IURIIVas/RVisitor/soft/src/tasks/motion_control/motion_control.h

/// \file motion_control.h
/// \brief mmm header files
/// \author 1jura.vas@gmail.com
///
/// \details
///

//--------------------------------------------------- Include guards ---------------------------------------------------

#ifndef MOTION_CONTROL_H_
#define MOTION_CONTROL_H_

//----------------------------------------------------- Includes -------------------------------------------------------

#include "global_inc.h"
#include "dc_motor_controller.h"

//------------------------------------------------------ Macros --------------------------------------------------------

//----------------------------------------------------- Typedefs -------------------------------------------------------

//---------------------------------------------------- Variables -------------------------------------------------------

extern TaskHandle_t motion_control_task_handler;

//------------------------------------------------ Function prototypes -------------------------------------------------

void motion_control_task_init(void);


#endif /* MOTION_CONTROL_H_ */
