IURIIVas/RVisitor/hardware/ch32v30x.h

/********************************** (C) COPYRIGHT  *******************************
* File Name          : ch32v30x.h
* Author             : WCH
* Version            : V1.0.0
* Date               : 2021/06/06
* Description        : CH32V30x Device Peripheral Access Layer Header File.
*********************************************************************************
* Copyright (c) 2021 Nanjing Qinheng Microelectronics Co., Ltd.
* Attention: This software (modified or not) and binary are used for 
* microcontroller manufactured by Nanjing Qinheng Microelectronics.
*******************************************************************************/  
#ifndef __CH32V30x_H
#define __CH32V30x_H

#ifdef __cplusplus
 extern "C" {
#endif 

#if !defined(CH32V30x_D8) && !defined(CH32V30x_D8C)
//#define CH32V30x_D8              /* CH32V303x */
#define CH32V30x_D8C             /* CH32V307x-CH32V305x */

#endif
  
#define __MPU_PRESENT             0 /* Other CH32 devices does not provide an MPU */
#define __Vendor_SysTickConfig    0 /* Set to 1 if different SysTick Config is used */	 
	 
#define HSE_VALUE    ((uint32_t)8000000) /* Value of the External oscillator in Hz */

/* In the following line adjust the External High Speed oscillator (HSE) Startup Timeout value */
#define HSE_STARTUP_TIMEOUT   ((uint16_t)0x1000) /* Time out for HSE start up */

#define HSI_VALUE    ((uint32_t)8000000) /* Value of the Internal oscillator in Hz */

/* CH32V30x Standard Peripheral Library version number */
#define __CH32V30x_STDPERIPH_VERSION_MAIN   (0x02) /* [15:8] main version */
#define __CH32V30x_STDPERIPH_VERSION_SUB    (0x01) /* [7:0] sub version */
#define __CH32V30x_STDPERIPH_VERSION        ( (__CH32V30x_STDPERIPH_VERSION_MAIN << 8)\
                                             |(__CH32V30x_STDPERIPH_VERSION_SUB << 0))


/* Interrupt Number Definition, according to the selected device */	 
typedef enum IRQn
{
 /******  RISC-V Processor Exceptions Numbers *******************************************************/
  NonMaskableInt_IRQn         = 2,       /* 2 Non Maskable Interrupt                             */
  EXC_IRQn                    = 3,       /* 3 Exception Interrupt                                */
  Ecall_M_Mode_IRQn           = 5,       /* 5 Ecall M Mode Interrupt                             */
  Ecall_U_Mode_IRQn           = 8,       /* 8 Ecall U Mode Interrupt                             */
  Break_Point_IRQn            = 9,       /* 9 Break Point Interrupt                              */
  SysTicK_IRQn                = 12,      /* 12 System timer Interrupt                            */
  Software_IRQn               = 14,      /* 14 software Interrupt                                */

 /******  RISC-V specific Interrupt Numbers *********************************************************/
  WWDG_IRQn                   = 16,      /* Window WatchDog Interrupt                            */
  PVD_IRQn                    = 17,      /* PVD through EXTI Line detection Interrupt            */
  TAMPER_IRQn                 = 18,      /* Tamper Interrupt                                     */
  RTC_IRQn                    = 19,      /* RTC global Interrupt                                 */
  FLASH_IRQn                  = 20,      /* FLASH global Interrupt                               */
  RCC_IRQn                    = 21,      /* RCC global Interrupt                                 */
  EXTI0_IRQn                  = 22,      /* EXTI Line0 Interrupt                                 */
  EXTI1_IRQn                  = 23,      /* EXTI Line1 Interrupt                                 */
  EXTI2_IRQn                  = 24,      /* EXTI Line2 Interrupt                                 */
  EXTI3_IRQn                  = 25,      /* EXTI Line3 Interrupt                                 */
  EXTI4_IRQn                  = 26,      /* EXTI Line4 Interrupt                                 */
  DMA1_Channel1_IRQn          = 27,      /* DMA1 Channel 1 global Interrupt                      */
  DMA1_Channel2_IRQn          = 28,      /* DMA1 Channel 2 global Interrupt                      */
  DMA1_Channel3_IRQn          = 29,      /* DMA1 Channel 3 global Interrupt                      */
  DMA1_Channel4_IRQn          = 30,      /* DMA1 Channel 4 global Interrupt                      */
  DMA1_Channel5_IRQn          = 31,      /* DMA1 Channel 5 global Interrupt                      */
  DMA1_Channel6_IRQn          = 32,      /* DMA1 Channel 6 global Interrupt                      */
  DMA1_Channel7_IRQn          = 33,      /* DMA1 Channel 7 global Interrupt                      */
  ADC_IRQn                    = 34,      /* ADC1 and ADC2 global Interrupt                       */
  USB_HP_CAN1_TX_IRQn         = 35,      /* USB Device High Priority or CAN1 TX Interrupts       */
  USB_LP_CAN1_RX0_IRQn        = 36,      /* USB Device Low Priority or CAN1 RX0 Interrupts       */
  CAN1_RX1_IRQn               = 37,      /* CAN1 RX1 Interrupt                                   */
  CAN1_SCE_IRQn               = 38,      /* CAN1 SCE Interrupt                                   */
  EXTI9_5_IRQn                = 39,      /* External Line[9:5] Interrupts                        */
  TIM1_BRK_IRQn               = 40,      /* TIM1 Break Interrupt                                 */
  TIM1_UP_IRQn                = 41,      /* TIM1 Update Interrupt                                */
  TIM1_TRG_COM_IRQn           = 42,      /* TIM1 Trigger and Commutation Interrupt               */
  TIM1_CC_IRQn                = 43,      /* TIM1 Capture Compare Interrupt                       */
  TIM2_IRQn                   = 44,      /* TIM2 global Interrupt                                */
  TIM3_IRQn                   = 45,      /* TIM3 global Interrupt                                */
  TIM4_IRQn                   = 46,      /* TIM4 global Interrupt                                */
  I2C1_EV_IRQn                = 47,      /* I2C1 Event Interrupt                                 */
  I2C1_ER_IRQn                = 48,      /* I2C1 Error Interrupt                                 */
  I2C2_EV_IRQn                = 49,      /* I2C2 Event Interrupt                                 */
  I2C2_ER_IRQn                = 50,      /* I2C2 Error Interrupt                                 */
  SPI1_IRQn                   = 51,      /* SPI1 global Interrupt                                */
  SPI2_IRQn                   = 52,      /* SPI2 global Interrupt                                */
  USART1_IRQn                 = 53,      /* USART1 global Interrupt                              */
  USART2_IRQn                 = 54,      /* USART2 global Interrupt                              */
  USART3_IRQn                 = 55,      /* USART3 global Interrupt                              */
  EXTI15_10_IRQn              = 56,      /* External Line[15:10] Interrupts                      */
  RTCAlarm_IRQn               = 57,      /* RTC Alarm through EXTI Line Interrupt                */

#ifdef CH32V30x_D8
  TIM8_BRK_IRQn               = 59,      /* TIM8 Break Interrupt                                 */
  TIM8_UP_IRQn                = 60,      /* TIM8 Update Interrupt                                */
  TIM8_TRG_COM_IRQn           = 61,      /* TIM8 Trigger and Commutation Interrupt               */
  TIM8_CC_IRQn                = 62,      /* TIM8 Capture Compare Interrupt                       */
  RNG_IRQn                    = 63,      /* RNG global Interrupt                                 */
  FSMC_IRQn                   = 64,      /* FSMC global Interrupt                                */
  SDIO_IRQn                   = 65,      /* SDIO global Interrupt                                */
  TIM5_IRQn                   = 66,      /* TIM5 global Interrupt                                */
  SPI3_IRQn                   = 67,      /* SPI3 global Interrupt                                */
  UART4_IRQn                  = 68,      /* UART4 global Interrupt                               */
  UART5_IRQn                  = 69,      /* UART5 global Interrupt                               */
  TIM6_IRQn                   = 70,      /* TIM6 global Interrupt                                */
  TIM7_IRQn                   = 71,      /* TIM7 global Interrupt                                */
  DMA2_Channel1_IRQn          = 72,      /* DMA2 Channel 1 global Interrupt                      */
  DMA2_Channel2_IRQn          = 73,      /* DMA2 Channel 2 global Interrupt                      */
  DMA2_Channel3_IRQn          = 74,      /* DMA2 Channel 3 global Interrupt                      */
  DMA2_Channel4_IRQn          = 75,      /* DMA2 Channel 4 global Interrupt                      */
  DMA2_Channel5_IRQn          = 76,      /* DMA2 Channel 5 global Interrupt                      */
  OTG_FS_IRQn                 = 83,      /* OTGFS global Interrupt                               */
  UART6_IRQn                  = 87,      /* UART6 global Interrupt                               */
  UART7_IRQn                  = 88,      /* UART7 global Interrupt                               */
  UART8_IRQn                  = 89,      /* UART8 global Interrupt                               */
  TIM9_BRK_IRQn               = 90,      /* TIM9 Break Interrupt                                 */
  TIM9_UP_IRQn                = 91,      /* TIM9 Update Interrupt                                */
  TIM9_TRG_COM_IRQn           = 92,      /* TIM9 Trigger and Commutation Interrupt               */
  TIM9_CC_IRQn                = 93,      /* TIM9 Capture Compare Interrupt                       */
  TIM10_BRK_IRQn              = 94,      /* TIM10 Break Interrupt                                */
  TIM10_UP_IRQn               = 95,      /* TIM10 Update Interrupt                               */
  TIM10_TRG_COM_IRQn          = 96,      /* TIM10 Trigger and Commutation Interrupt              */
  TIM10_CC_IRQn               = 97,      /* TIM10 Capture Compare Interrupt                      */
  DMA2_Channel6_IRQn          = 98,      /* DMA2 Channel 6 global Interrupt                      */
  DMA2_Channel7_IRQn          = 99,      /* DMA2 Channel 7 global Interrupt                      */
  DMA2_Channel8_IRQn          = 100,     /* DMA2 Channel 8 global Interrupt                      */
  DMA2_Channel9_IRQn          = 101,     /* DMA2 Channel 9 global Interrupt                      */
  DMA2_Channel10_IRQn         = 102,     /* DMA2 Channel 10 global Interrupt                     */
  DMA2_Channel11_IRQn         = 103,     /* DMA2 Channel 11 global Interrupt                     */

#elif defined  (CH32V30x_D8C)
  USBWakeUp_IRQn              = 58,      /* USB Device WakeUp from suspend through EXTI Line Interrupt */
  TIM8_BRK_IRQn               = 59,      /* TIM8 Break Interrupt                                 */
  TIM8_UP_IRQn                = 60,      /* TIM8 Update Interrupt                                */
  TIM8_TRG_COM_IRQn           = 61,      /* TIM8 Trigger and Commutation Interrupt               */
  TIM8_CC_IRQn                = 62,      /* TIM8 Capture Compare Interrupt                       */
  RNG_IRQn                    = 63,      /* RNG global Interrupt                                 */
  FSMC_IRQn                   = 64,      /* FSMC global Interrupt                                */
  SDIO_IRQn                   = 65,      /* SDIO global Interrupt                                */
  TIM5_IRQn                   = 66,      /* TIM5 global Interrupt                                */
  SPI3_IRQn                   = 67,      /* SPI3 global Interrupt                                */
  UART4_IRQn                  = 68,      /* UART4 global Interrupt                               */
  UART5_IRQn                  = 69,      /* UART5 global Interrupt                               */
  TIM6_IRQn                   = 70,      /* TIM6 global Interrupt                                */
  TIM7_IRQn                   = 71,      /* TIM7 global Interrupt                                */
  DMA2_Channel1_IRQn          = 72,      /* DMA2 Channel 1 global Interrupt                      */
  DMA2_Channel2_IRQn          = 73,      /* DMA2 Channel 2 global Interrupt                      */
  DMA2_Channel3_IRQn          = 74,      /* DMA2 Channel 3 global Interrupt                      */
  DMA2_Channel4_IRQn          = 75,      /* DMA2 Channel 4 global Interrupt                      */
  DMA2_Channel5_IRQn          = 76,      /* DMA2 Channel 5 global Interrupt                      */
  ETH_IRQn                    = 77,      /* ETH global Interrupt                                 */
  ETH_WKUP_IRQn               = 78,      /* ETH WakeUp Interrupt                                 */
  CAN2_TX_IRQn                = 79,      /* CAN2 TX Interrupts                                   */
  CAN2_RX0_IRQn               = 80,      /* CAN2 RX0 Interrupts                                  */
  CAN2_RX1_IRQn               = 81,      /* CAN2 RX1 Interrupt                                   */
  CAN2_SCE_IRQn               = 82,      /* CAN2 SCE Interrupt                                   */
  OTG_FS_IRQn                 = 83,      /* OTGFS global Interrupt                               */
  USBHSWakeup_IRQn            = 84,      /* USBHS WakeUp Interrupt                               */
  USBHS_IRQn                  = 85,      /* USBHS global Interrupt                               */
  DVP_IRQn                    = 86,      /* DVP global Interrupt                                 */
  UART6_IRQn                  = 87,      /* UART6 global Interrupt                               */
  UART7_IRQn                  = 88,      /* UART7 global Interrupt                               */
  UART8_IRQn                  = 89,      /* UART8 global Interrupt                               */
  TIM9_BRK_IRQn               = 90,      /* TIM9 Break Interrupt                                 */
  TIM9_UP_IRQn                = 91,      /* TIM9 Update Interrupt                                */
  TIM9_TRG_COM_IRQn           = 92,      /* TIM9 Trigger and Commutation Interrupt               */
  TIM9_CC_IRQn                = 93,      /* TIM9 Capture Compare Interrupt                       */
  TIM10_BRK_IRQn              = 94,      /* TIM10 Break Interrupt                                */
  TIM10_UP_IRQn               = 95,      /* TIM10 Update Interrupt                               */
  TIM10_TRG_COM_IRQn          = 96,      /* TIM10 Trigger and Commutation Interrupt              */
  TIM10_CC_IRQn               = 97,      /* TIM10 Capture Compare Interrupt                      */
  DMA2_Channel6_IRQn          = 98,      /* DMA2 Channel 6 global Interrupt                      */
  DMA2_Channel7_IRQn          = 99,      /* DMA2 Channel 7 global Interrupt                      */
  DMA2_Channel8_IRQn          = 100,     /* DMA2 Channel 8 global Interrupt                      */
  DMA2_Channel9_IRQn          = 101,     /* DMA2 Channel 9 global Interrupt                      */
  DMA2_Channel10_IRQn         = 102,     /* DMA2 Channel 10 global Interrupt                     */
  DMA2_Channel11_IRQn         = 103,     /* DMA2 Channel 11 global Interrupt                     */

#endif
} irqn_e;

#define HardFault_IRQn   EXC_IRQn
#define ADC1_2_IRQn      ADC_IRQn


#include <stdint.h>
#include "core_riscv.h"
#include "system_ch32v30x.h"


/* Standard Peripheral Library old definitions (maintained for legacy purpose) */
#define HSI_Value            HSI_VALUE 
#define HSE_Value            HSE_VALUE
#define HSEStartUp_TimeOut   HSE_STARTUP_TIMEOUT

/* Analog to Digital Converter */
typedef struct
{
  __RW uint32_t STATR;
  __RW uint32_t CTLR1;
  __RW uint32_t CTLR2;
  __RW uint32_t SAMPTR1;
  __RW uint32_t SAMPTR2;
  __RW uint32_t IOFR1;
  __RW uint32_t IOFR2;
  __RW uint32_t IOFR3;
  __RW uint32_t IOFR4;
  __RW uint32_t WDHTR;
  __RW uint32_t WDLTR;
  __RW uint32_t RSQR1;
  __RW uint32_t RSQR2;
  __RW uint32_t RSQR3;
  __RW uint32_t ISQR;
  __RW uint32_t IDATAR1;
  __RW uint32_t IDATAR2;
  __RW uint32_t IDATAR3;
  __RW uint32_t IDATAR4;
  __RW uint32_t RDATAR;
} ADC_TypeDef;

/* Backup Registers */
typedef struct
{
  uint32_t  RESERVED0;
  __RW uint16_t DATAR1;
  uint16_t  RESERVED1;
  __RW uint16_t DATAR2;
  uint16_t  RESERVED2;
  __RW uint16_t DATAR3;
  uint16_t  RESERVED3;
  __RW uint16_t DATAR4;
  uint16_t  RESERVED4;
  __RW uint16_t DATAR5;
  uint16_t  RESERVED5;
  __RW uint16_t DATAR6;
  uint16_t  RESERVED6;
  __RW uint16_t DATAR7;
  uint16_t  RESERVED7;
  __RW uint16_t DATAR8;
  uint16_t  RESERVED8;
  __RW uint16_t DATAR9;
  uint16_t  RESERVED9;
  __RW uint16_t DATAR10;
  uint16_t  RESERVED10; 
  __RW uint16_t OCTLR;
  uint16_t  RESERVED11;
  __RW uint16_t TPCTLR;
  uint16_t  RESERVED12;
  __RW uint16_t TPCSR;
  uint16_t  RESERVED13[5];
  __RW uint16_t DATAR11;
  uint16_t  RESERVED14;
  __RW uint16_t DATAR12;
  uint16_t  RESERVED15;
  __RW uint16_t DATAR13;
  uint16_t  RESERVED16;
  __RW uint16_t DATAR14;
  uint16_t  RESERVED17;
  __RW uint16_t DATAR15;
  uint16_t  RESERVED18;
  __RW uint16_t DATAR16;
  uint16_t  RESERVED19;
  __RW uint16_t DATAR17;
  uint16_t  RESERVED20;
  __RW uint16_t DATAR18;
  uint16_t  RESERVED21;
  __RW uint16_t DATAR19;
  uint16_t  RESERVED22;
  __RW uint16_t DATAR20;
  uint16_t  RESERVED23;
  __RW uint16_t DATAR21;
  uint16_t  RESERVED24;
  __RW uint16_t DATAR22;
  uint16_t  RESERVED25;
  __RW uint16_t DATAR23;
  uint16_t  RESERVED26;
  __RW uint16_t DATAR24;
  uint16_t  RESERVED27;
  __RW uint16_t DATAR25;
  uint16_t  RESERVED28;
  __RW uint16_t DATAR26;
  uint16_t  RESERVED29;
  __RW uint16_t DATAR27;
  uint16_t  RESERVED30;
  __RW uint16_t DATAR28;
  uint16_t  RESERVED31;
  __RW uint16_t DATAR29;
  uint16_t  RESERVED32;
  __RW uint16_t DATAR30;
  uint16_t  RESERVED33; 
  __RW uint16_t DATAR31;
  uint16_t  RESERVED34;
  __RW uint16_t DATAR32;
  uint16_t  RESERVED35;
  __RW uint16_t DATAR33;
  uint16_t  RESERVED36;
  __RW uint16_t DATAR34;
  uint16_t  RESERVED37;
  __RW uint16_t DATAR35;
  uint16_t  RESERVED38;
  __RW uint16_t DATAR36;
  uint16_t  RESERVED39;
  __RW uint16_t DATAR37;
  uint16_t  RESERVED40;
  __RW uint16_t DATAR38;
  uint16_t  RESERVED41;
  __RW uint16_t DATAR39;
  uint16_t  RESERVED42;
  __RW uint16_t DATAR40;
  uint16_t  RESERVED43;
  __RW uint16_t DATAR41;
  uint16_t  RESERVED44;
  __RW uint16_t DATAR42;
  uint16_t  RESERVED45;    
} BKP_TypeDef;

/* Controller Area Network TxMailBox */
typedef struct
{
  __RW uint32_t TXMIR;
  __RW uint32_t TXMDTR;
  __RW uint32_t TXMDLR;
  __RW uint32_t TXMDHR;
} CAN_TxMailBox_TypeDef;

/* Controller Area Network FIFOMailBox */ 
typedef struct
{
  __RW uint32_t RXMIR;
  __RW uint32_t RXMDTR;
  __RW uint32_t RXMDLR;
  __RW uint32_t RXMDHR;
} CAN_FIFOMailBox_TypeDef;

/* Controller Area Network FilterRegister */  
typedef struct
{
  __RW uint32_t FR1;
  __RW uint32_t FR2;
} CAN_FilterRegister_TypeDef;

/* Controller Area Network */  
typedef struct
{
  __RW uint32_t CTLR;
  __RW uint32_t STATR;
  __RW uint32_t TSTATR;
  __RW uint32_t RFIFO0;
  __RW uint32_t RFIFO1;
  __RW uint32_t INTENR;
  __RW uint32_t ERRSR;
  __RW uint32_t BTIMR;
  uint32_t  RESERVED0[88];
  CAN_TxMailBox_TypeDef sTxMailBox[3];
  CAN_FIFOMailBox_TypeDef sFIFOMailBox[2];
  uint32_t  RESERVED1[12];
  __RW uint32_t FCTLR;
  __RW uint32_t FMCFGR;
  uint32_t  RESERVED2;
  __RW uint32_t FSCFGR;
  uint32_t  RESERVED3;
  __RW uint32_t FAFIFOR;
  uint32_t  RESERVED4;
  __RW uint32_t FWR;
  uint32_t  RESERVED5[8];
  CAN_FilterRegister_TypeDef sFilterRegister[28];
} CAN_TypeDef;

/* CRC Calculation Unit */
typedef struct
{
  __RW uint32_t DATAR;
  __RW uint8_t  IDATAR;
  uint8_t   RESERVED0;
  uint16_t  RESERVED1;
  __RW uint32_t CTLR;
} CRC_TypeDef;

/* Digital to Analog Converter */
typedef struct
{
  __RW uint32_t CTLR;
  __RW uint32_t SWTR;
  __RW uint32_t R12BDHR1;
  __RW uint32_t L12BDHR1;
  __RW uint32_t R8BDHR1;
  __RW uint32_t R12BDHR2;
  __RW uint32_t L12BDHR2;
  __RW uint32_t R8BDHR2;
  __RW uint32_t RD12BDHR;
  __RW uint32_t LD12BDHR;
  __RW uint32_t RD8BDHR;
  __RW uint32_t DOR1;
  __RW uint32_t DOR2;
} DAC_TypeDef;

/* DMA Channel Controller */
typedef struct
{
  __RW uint32_t CFGR;
  __RW uint32_t CNTR;
  __RW uint32_t PADDR;
  __RW uint32_t MADDR;
} DMA_Channel_TypeDef;

/* DMA Controller */
typedef struct
{
  __RW uint32_t INTFR;
  __RW uint32_t INTFCR;
} DMA_TypeDef;

/* External Interrupt/Event Controller */
typedef struct
{
  __RW uint32_t INTENR; 
  __RW uint32_t EVENR;   
  __RW uint32_t RTENR;   
  __RW uint32_t FTENR;   
  __RW uint32_t SWIEVR;  
  __RW uint32_t INTFR;   
} EXTI_TypeDef;

/* FLASH Registers */
typedef struct
{
  __RW uint32_t ACTLR;
  __RW uint32_t KEYR;
  __RW uint32_t OBKEYR;
  __RW uint32_t STATR;
  __RW uint32_t CTLR;
  __RW uint32_t ADDR;
  __RW uint32_t RESERVED;
  __RW uint32_t OBR;
  __RW uint32_t WPR;
  __RW uint32_t MODEKEYR;
} FLASH_TypeDef;

/* Option Bytes Registers */  
typedef struct
{
  __RW uint16_t RDPR;
  __RW uint16_t USER;
  __RW uint16_t Data0;
  __RW uint16_t Data1;
  __RW uint16_t WRPR0;
  __RW uint16_t WRPR1;
  __RW uint16_t WRPR2;
  __RW uint16_t WRPR3;
} OB_TypeDef;

/* FSMC Bank1 Registers */ 
typedef struct
{
  __RW uint32_t BTCR[8];
} FSMC_Bank1_TypeDef;

/* FSMC Bank1E Registers */ 
typedef struct
{
  __RW uint32_t BWTR[7];
} FSMC_Bank1E_TypeDef;

/* FSMC Bank2 Registers */ 
typedef struct
{
  __RW uint32_t PCR2;
  __RW uint32_t SR2;
  __RW uint32_t PMEM2;
  __RW uint32_t PATT2;
  uint32_t  RESERVED0;
  __RW uint32_t ECCR2;
} FSMC_Bank2_TypeDef;

/* General Purpose I/O */
typedef struct
{
  __RW uint32_t CFGLR;
  __RW uint32_t CFGHR;
  __RW uint32_t INDR;
  __RW uint32_t OUTDR;
  __RW uint32_t BSHR;
  __RW uint32_t BCR;
  __RW uint32_t LCKR;
} gpio_s;

/* Alternate Function I/O */
typedef struct
{
  __RW uint32_t ECR;
  __RW uint32_t PCFR1;
  __RW uint32_t EXTICR[4];
  uint32_t RESERVED0;
  __RW uint32_t PCFR2;  
} AFIO_TypeDef;

/* Inter Integrated Circuit Interface */
typedef struct
{
  __RW uint16_t CTLR1;
  uint16_t  RESERVED0;
  __RW uint16_t CTLR2;
  uint16_t  RESERVED1;
  __RW uint16_t OADDR1;
  uint16_t  RESERVED2;
  __RW uint16_t OADDR2;
  uint16_t  RESERVED3;
  __RW uint16_t DATAR;
  uint16_t  RESERVED4;
  __RW uint16_t STAR1;
  uint16_t  RESERVED5;
  __RW uint16_t STAR2;
  uint16_t  RESERVED6;
  __RW uint16_t CKCFGR;
  uint16_t  RESERVED7;
  __RW uint16_t RTR;
  uint16_t  RESERVED8;
} i2c_s;

/* Independent WatchDog */
typedef struct
{
  __RW uint32_t CTLR;
  __RW uint32_t PSCR;
  __RW uint32_t RLDR;
  __RW uint32_t STATR;
} IWDG_TypeDef;

/* Power Control */
typedef struct
{
  __RW uint32_t CTLR;
  __RW uint32_t CSR;
} PWR_TypeDef;

/* Reset and Clock Control */
typedef struct
{
  __RW uint32_t CTLR;
  __RW uint32_t CFGR0;
  __RW uint32_t INTR;
  __RW uint32_t APB2PRSTR;
  __RW uint32_t APB1PRSTR;
  __RW uint32_t AHBPCENR;
  __RW uint32_t APB2PCENR;
  __RW uint32_t APB1PCENR;
  __RW uint32_t BDCTLR;
  __RW uint32_t RSTSCKR;

  __RW uint32_t AHBRSTR;
  __RW uint32_t CFGR2;
} RCC_TypeDef;

/* Real-Time Clock */
typedef struct
{
  __RW uint16_t CTLRH;
  uint16_t  RESERVED0;
  __RW uint16_t CTLRL;
  uint16_t  RESERVED1;
  __RW uint16_t PSCRH;
  uint16_t  RESERVED2;
  __RW uint16_t PSCRL;
  uint16_t  RESERVED3;
  __RW uint16_t DIVH;
  uint16_t  RESERVED4;
  __RW uint16_t DIVL;
  uint16_t  RESERVED5;
  __RW uint16_t CNTH;
  uint16_t  RESERVED6;
  __RW uint16_t CNTL;
  uint16_t  RESERVED7;
  __RW uint16_t ALRMH;
  uint16_t  RESERVED8;
  __RW uint16_t ALRML;
  uint16_t  RESERVED9;
} RTC_TypeDef;

/* SDIO Registers */ 
typedef struct
{
  __RW uint32_t POWER;
  __RW uint32_t CLKCR;
  __RW uint32_t ARG;
  __RW uint32_t CMD;
  __RO uint32_t RESPCMD;
  __RO uint32_t RESP1;
  __RO uint32_t RESP2;
  __RO uint32_t RESP3;
  __RO uint32_t RESP4;
  __RW uint32_t DTIMER;
  __RW uint32_t DLEN;
  __RW uint32_t DCTRL;
  __RO uint32_t DCOUNT;
  __RO uint32_t STA;
  __RW uint32_t ICR;
  __RW uint32_t MASK;
  uint32_t  RESERVED0[2];
  __RO uint32_t FIFOCNT;
  uint32_t  RESERVED1[13];
  __RW uint32_t FIFO;
} SDIO_TypeDef;

/* Serial Peripheral Interface */
typedef struct
{
  __RW uint16_t CTLR1;
  uint16_t  RESERVED0;
  __RW uint16_t CTLR2;
  uint16_t  RESERVED1;
  __RW uint16_t STATR;
  uint16_t  RESERVED2;
  __RW uint16_t DATAR;
  uint16_t  RESERVED3;
  __RW uint16_t CRCR;
  uint16_t  RESERVED4;
  __RW uint16_t RCRCR;
  uint16_t  RESERVED5;
  __RW uint16_t TCRCR;
  uint16_t  RESERVED6;
  __RW uint16_t I2SCFGR;
  uint16_t  RESERVED7;
  __RW uint16_t I2SPR;
  uint16_t  RESERVED8;
  __RW uint16_t HSCR;
  uint16_t  RESERVED9;
} spi_s;

/* TIM */
typedef struct
{
  __RW uint16_t CTLR1;
  uint16_t  RESERVED0;
  __RW uint16_t CTLR2;
  uint16_t  RESERVED1;
  __RW uint16_t SMCFGR;
  uint16_t  RESERVED2;
  __RW uint16_t DMAINTENR;
  uint16_t  RESERVED3;
  __RW uint16_t INTFR;
  uint16_t  RESERVED4;
  __RW uint16_t SWEVGR;
  uint16_t  RESERVED5;
  __RW uint16_t CHCTLR1;
  uint16_t  RESERVED6;
  __RW uint16_t CHCTLR2;
  uint16_t  RESERVED7;
  __RW uint16_t CCER;
  uint16_t  RESERVED8;
  __RW uint16_t CNT;
  uint16_t  RESERVED9;
  __RW uint16_t PSC;
  uint16_t  RESERVED10;
  __RW uint16_t ATRLR;
  uint16_t  RESERVED11;
  __RW uint16_t RPTCR;
  uint16_t  RESERVED12;
  __RW uint16_t CH1CVR;
  uint16_t  RESERVED13;
  __RW uint16_t CH2CVR;
  uint16_t  RESERVED14;
  __RW uint16_t CH3CVR;
  uint16_t  RESERVED15;
  __RW uint16_t CH4CVR;
  uint16_t  RESERVED16;
  __RW uint16_t BDTR;
  uint16_t  RESERVED17;
  __RW uint16_t DMACFGR;
  uint16_t  RESERVED18;
  __RW uint16_t DMAADR;
  uint16_t  RESERVED19;
} TIM_TypeDef;

/* Universal Synchronous Asynchronous Receiver Transmitter */
typedef struct
{
  __RW uint16_t STATR;
  uint16_t  RESERVED0;
  __RW uint16_t DATAR;
  uint16_t  RESERVED1;
  __RW uint16_t BRR;
  uint16_t  RESERVED2;
  __RW uint16_t CTLR1;
  uint16_t  RESERVED3;
  __RW uint16_t CTLR2;
  uint16_t  RESERVED4;
  __RW uint16_t CTLR3;
  uint16_t  RESERVED5;
  __RW uint16_t GPR;
  uint16_t  RESERVED6;
} USART_TypeDef;

/* Window WatchDog */
typedef struct
{
  __RW uint32_t CTLR;
  __RW uint32_t CFGR;
  __RW uint32_t STATR;
} WWDG_TypeDef;

/* Enhanced Registers */
typedef struct
{
  __RW uint32_t EXTEN_CTR;
} EXTEN_TypeDef;

/* OPA Registers */
typedef struct
{
  __RW uint32_t CR;
} OPA_TypeDef;

/* RNG Registers */
typedef struct
{
  __RW uint32_t CR;
  __RW uint32_t SR;
  __RW uint32_t DR;
} RNG_TypeDef;

/* DVP Registers */
typedef struct
{
  __RW uint8_t CR0;
  __RW uint8_t CR1;
  __RW uint8_t IER;
  __RW uint8_t Reserved0;        
  __RW uint16_t ROW_NUM;
  __RW uint16_t COL_NUM;
  __RW uint32_t DMA_BUF0;
  __RW uint32_t DMA_BUF1;
  __RW uint8_t IFR;
  __RW uint8_t STATUS;
  __RW uint16_t Reserved1;            
  __RW uint16_t ROW_CNT;
  __RW uint16_t Reserved2;           
  __RW uint16_t HOFFCNT;
  __RW uint16_t VST;
  __RW uint16_t CAPCNT;
  __RW uint16_t VLINE;
  __RW uint32_t DR;
} DVP_TypeDef;

/* USBHS Registers */
typedef struct
{
  __RW uint8_t  CONTROL;
  __RW uint8_t  HOST_CTRL;
  __RW uint8_t  INT_EN;
  __RW uint8_t  DEV_AD;
  __RW uint16_t FRAME_NO;
  __RW uint8_t  SUSPEND;
  __RW uint8_t  RESERVED0;
  __RW uint8_t  SPEED_TYPE;
  __RW uint8_t  MIS_ST;
  __RW uint8_t  INT_FG;
  __RW uint8_t  INT_ST;
  __RW uint16_t RX_LEN;
  __RW uint16_t RESERVED1;
  __RW uint32_t ENDP_CONFIG;
  __RW uint32_t ENDP_TYPE;
  __RW uint32_t BUF_MODE;
  __RW uint32_t UEP0_DMA;               
  __RW uint32_t UEP1_RX_DMA;       
  __RW uint32_t UEP2_RX_DMA;       
  __RW uint32_t UEP3_RX_DMA;       
  __RW uint32_t UEP4_RX_DMA;       
  __RW uint32_t UEP5_RX_DMA;       
  __RW uint32_t UEP6_RX_DMA;       
  __RW uint32_t UEP7_RX_DMA;       
  __RW uint32_t UEP8_RX_DMA;      
  __RW uint32_t UEP9_RX_DMA;       
  __RW uint32_t UEP10_RX_DMA;      
  __RW uint32_t UEP11_RX_DMA;      
  __RW uint32_t UEP12_RX_DMA;      
  __RW uint32_t UEP13_RX_DMA;      
  __RW uint32_t UEP14_RX_DMA;      
  __RW uint32_t UEP15_RX_DMA;      
  __RW uint32_t UEP1_TX_DMA;       
  __RW uint32_t UEP2_TX_DMA;       
  __RW uint32_t UEP3_TX_DMA;       
  __RW uint32_t UEP4_TX_DMA;       
  __RW uint32_t UEP5_TX_DMA;      
  __RW uint32_t UEP6_TX_DMA;      
  __RW uint32_t UEP7_TX_DMA;       
  __RW uint32_t UEP8_TX_DMA;      
  __RW uint32_t UEP9_TX_DMA;       
  __RW uint32_t UEP10_TX_DMA;      
  __RW uint32_t UEP11_TX_DMA;      
  __RW uint32_t UEP12_TX_DMA;    
  __RW uint32_t UEP13_TX_DMA;      
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
    __RW uint32_t RESERVED42;
    __RW uint32_t RESERVED43;
    __RW uint32_t RESERVED44;
    __RW uint32_t RESERVED45;
    __RW uint32_t RESERVED46;
    __RW uint32_t RESERVED47;
    __RW uint32_t RESERVED48;
    __RW uint32_t RESERVED49;
    __RW uint8_t  HOST_EP_PID;
    __RW uint8_t  RESERVED50;
    __RW uint8_t  RESERVED51;
    __RW uint8_t  HOST_RX_CTRL;
    __RW uint16_t HOST_TX_LEN;
    __RW uint8_t  HOST_TX_CTRL;
    __RW uint8_t  RESERVED52;
    __RW uint16_t HOST_SPLIT_DATA;
} USBHSH_TypeDef;


/* USBOTG_FS Registers */
typedef struct
{
   __RW uint8_t  BASE_CTRL;
   __RW uint8_t  UDEV_CTRL;
   __RW uint8_t  INT_EN;
   __RW uint8_t  DEV_ADDR;
   __RW uint8_t  Reserve0;
   __RW uint8_t  MIS_ST;
   __RW uint8_t  INT_FG;
   __RW uint8_t  INT_ST;
   __RW uint16_t RX_LEN;
   __RW uint16_t Reserve1;
   __RW uint8_t  UEP4_1_MOD;
   __RW uint8_t  UEP2_3_MOD;
   __RW uint8_t  UEP5_6_MOD;
   __RW uint8_t  UEP7_MOD;
   __RW uint32_t UEP0_DMA;
   __RW uint32_t UEP1_DMA;
   __RW uint32_t UEP2_DMA;
   __RW uint32_t UEP3_DMA;
   __RW uint32_t UEP4_DMA;
   __RW uint32_t UEP5_DMA;
   __RW uint32_t UEP6_DMA;
   __RW uint32_t UEP7_DMA;
   __RW uint16_t UEP0_TX_LEN;
   __RW uint8_t  UEP0_TX_CTRL;
   __RW uint8_t  UEP0_RX_CTRL;
   __RW uint16_t UEP1_TX_LEN;
   __RW uint8_t  UEP1_TX_CTRL;
   __RW uint8_t  UEP1_RX_CTRL;
   __RW uint16_t UEP2_TX_LEN;
   __RW uint8_t  UEP2_TX_CTRL;
   __RW uint8_t  UEP2_RX_CTRL;
   __RW uint16_t UEP3_TX_LEN;
   __RW uint8_t  UEP3_TX_CTRL;
   __RW uint8_t  UEP3_RX_CTRL;
   __RW uint16_t UEP4_TX_LEN;
   __RW uint8_t  UEP4_TX_CTRL;
   __RW uint8_t  UEP4_RX_CTRL;
   __RW uint16_t UEP5_TX_LEN;
   __RW uint8_t  UEP5_TX_CTRL;
   __RW uint8_t  UEP5_RX_CTRL;
   __RW uint16_t UEP6_TX_LEN;
   __RW uint8_t  UEP6_TX_CTRL;
   __RW uint8_t  UEP6_RX_CTRL;
   __RW uint16_t UEP7_TX_LEN;
   __RW uint8_t  UEP7_TX_CTRL;
   __RW uint8_t  UEP7_RX_CTRL;
   __RW uint32_t Reserve2;
   __RW uint32_t OTG_CR;
   __RW uint32_t OTG_SR;
}USBOTG_FS_TypeDef;

typedef struct  __attribute__((packed))
{
   __RW uint8_t   BASE_CTRL;
   __RW uint8_t   HOST_CTRL;
   __RW uint8_t   INT_EN;
   __RW uint8_t   DEV_ADDR;
   __RW uint8_t   Reserve0;
   __RW uint8_t   MIS_ST;
   __RW uint8_t   INT_FG;
   __RW uint8_t   INT_ST;
   __RW uint16_t  RX_LEN;
   __RW uint16_t  Reserve1;
   __RW uint8_t   Reserve2;
   __RW uint8_t   HOST_EP_MOD;
   __RW uint16_t  Reserve3;
   __RW uint32_t  Reserve4;
   __RW uint32_t  Reserve5;
   __RW uint32_t  HOST_RX_DMA;
   __RW uint32_t  HOST_TX_DMA;
   __RW uint32_t  Reserve6;
   __RW uint32_t  Reserve7;
   __RW uint32_t  Reserve8;
   __RW uint32_t  Reserve9;
   __RW uint32_t  Reserve10;
   __RW uint16_t  Reserve11;
   __RW uint16_t  HOST_SETUP;
   __RW uint8_t   HOST_EP_PID;
   __RW uint8_t   Reserve12;
   __RW uint8_t   Reserve13;
   __RW uint8_t   HOST_RX_CTRL;
   __RW uint16_t  HOST_TX_LEN;
   __RW uint8_t   HOST_TX_CTRL;
   __RW uint8_t   Reserve14;
   __RW uint32_t  Reserve15;
   __RW uint32_t  Reserve16;
   __RW uint32_t  Reserve17;
   __RW uint32_t  Reserve18;
   __RW uint32_t  Reserve19;
   __RW uint32_t  OTG_CR;
   __RW uint32_t  OTG_SR;
}USBOTGH_FS_TypeDef;

/* Ethernet MAC */
typedef struct
{
  __RW uint32_t MACCR;
  __RW uint32_t MACFFR;
  __RW uint32_t MACHTHR;
  __RW uint32_t MACHTLR;
  __RW uint32_t MACMIIAR;
  __RW uint32_t MACMIIDR;
  __RW uint32_t MACFCR;
  __RW uint32_t MACVLANTR;
       uint32_t RESERVED0[2];
  __RW uint32_t MACRWUFFR;
  __RW uint32_t MACPMTCSR;
       uint32_t RESERVED1[2];
  __RW uint32_t MACSR;
  __RW uint32_t MACIMR;
  __RW uint32_t MACA0HR;
  __RW uint32_t MACA0LR;
  __RW uint32_t MACA1HR;
  __RW uint32_t MACA1LR;
  __RW uint32_t MACA2HR;
  __RW uint32_t MACA2LR;
  __RW uint32_t MACA3HR;
  __RW uint32_t MACA3LR;
       uint32_t RESERVED2[40];
  __RW uint32_t MMCCR;
  __RW uint32_t MMCRIR;
  __RW uint32_t MMCTIR;
  __RW uint32_t MMCRIMR;
  __RW uint32_t MMCTIMR;
       uint32_t RESERVED3[14];
  __RW uint32_t MMCTGFSCCR;
  __RW uint32_t MMCTGFMSCCR;
       uint32_t RESERVED4[5];
  __RW uint32_t MMCTGFCR;
       uint32_t RESERVED5[10];
  __RW uint32_t MMCRFCECR;
  __RW uint32_t MMCRFAECR;
       uint32_t RESERVED6[10];
  __RW uint32_t MMCRGUFCR;
       uint32_t RESERVED7[334];
  __RW uint32_t PTPTSCR;
  __RW uint32_t PTPSSIR;
  __RW uint32_t PTPTSHR;
  __RW uint32_t PTPTSLR;
  __RW uint32_t PTPTSHUR;
  __RW uint32_t PTPTSLUR;
  __RW uint32_t PTPTSAR;
  __RW uint32_t PTPTTHR;
  __RW uint32_t PTPTTLR;
       uint32_t RESERVED8[567];
  __RW uint32_t DMABMR;
  __RW uint32_t DMATPDR;
  __RW uint32_t DMARPDR;
  __RW uint32_t DMARDLAR;
  __RW uint32_t DMATDLAR;
  __RW uint32_t DMASR;
  __RW uint32_t DMAOMR;
  __RW uint32_t DMAIER;
  __RW uint32_t DMAMFBOCR;
       uint32_t RESERVED9[9];
  __RW uint32_t DMACHTDR;
  __RW uint32_t DMACHRDR;
  __RW uint32_t DMACHTBAR;
  __RW uint32_t DMACHRBAR;
} ETH_TypeDef;



/* Peripheral memory map */
#define FLASH_BASE            ((uint32_t)0x08000000) /* FLASH base address in the alias region */
#define SRAM_BASE             ((uint32_t)0x20000000) /* SRAM base address in the alias region */
#define PERIPH_BASE           ((uint32_t)0x40000000) /* Peripheral base address in the alias region */

#define FSMC_R_BASE           ((uint32_t)0xA0000000) /* FSMC registers base address */


#define APB1PERIPH_BASE       (PERIPH_BASE)
#define APB2PERIPH_BASE       (PERIPH_BASE + 0x10000)
#define AHBPERIPH_BASE        (PERIPH_BASE + 0x20000)

#define TIM2_BASE             (APB1PERIPH_BASE + 0x0000)
#define TIM3_BASE             (APB1PERIPH_BASE + 0x0400)
#define TIM4_BASE             (APB1PERIPH_BASE + 0x0800)
#define TIM5_BASE             (APB1PERIPH_BASE + 0x0C00)
#define TIM6_BASE             (APB1PERIPH_BASE + 0x1000)
#define TIM7_BASE             (APB1PERIPH_BASE + 0x1400)
#define UART6_BASE            (APB1PERIPH_BASE + 0x1800)
#define UART7_BASE            (APB1PERIPH_BASE + 0x1C00)
#define UART8_BASE            (APB1PERIPH_BASE + 0x2000)
#define RTC_BASE              (APB1PERIPH_BASE + 0x2800)
#define WWDG_BASE             (APB1PERIPH_BASE + 0x2C00)
#define IWDG_BASE             (APB1PERIPH_BASE + 0x3000)
#define SPI2_BASE             (APB1PERIPH_BASE + 0x3800)
#define SPI3_BASE             (APB1PERIPH_BASE + 0x3C00)
#define USART2_BASE           (APB1PERIPH_BASE + 0x4400)
#define USART3_BASE           (APB1PERIPH_BASE + 0x4800)
#define UART4_BASE            (APB1PERIPH_BASE + 0x4C00)
#define UART5_BASE            (APB1PERIPH_BASE + 0x5000)
#define I2C1_BASE             (APB1PERIPH_BASE + 0x5400)
#define I2C2_BASE             (APB1PERIPH_BASE + 0x5800)
#define CAN1_BASE             (APB1PERIPH_BASE + 0x6400)
#define CAN2_BASE             (APB1PERIPH_BASE + 0x6800)
#define BKP_BASE              (APB1PERIPH_BASE + 0x6C00)
#define PWR_BASE              (APB1PERIPH_BASE + 0x7000)
#define DAC_BASE              (APB1PERIPH_BASE + 0x7400)

#define AFIO_BASE             (APB2PERIPH_BASE + 0x0000)
#define EXTI_BASE             (APB2PERIPH_BASE + 0x0400)
#define GPIOA_BASE            (APB2PERIPH_BASE + 0x0800)
#define GPIOB_BASE            (APB2PERIPH_BASE + 0x0C00)
#define GPIOC_BASE            (APB2PERIPH_BASE + 0x1000)
#define GPIOD_BASE            (APB2PERIPH_BASE + 0x1400)
#define GPIOE_BASE            (APB2PERIPH_BASE + 0x1800)
#define GPIOF_BASE            (APB2PERIPH_BASE + 0x1C00)
#define GPIOG_BASE            (APB2PERIPH_BASE + 0x2000)
#define ADC1_BASE             (APB2PERIPH_BASE + 0x2400)
#define ADC2_BASE             (APB2PERIPH_BASE + 0x2800)
#define TIM1_BASE             (APB2PERIPH_BASE + 0x2C00)
#define SPI1_BASE             (APB2PERIPH_BASE + 0x3000)
#define TIM8_BASE             (APB2PERIPH_BASE + 0x3400)
#define USART1_BASE           (APB2PERIPH_BASE + 0x3800)
#define ADC3_BASE             (APB2PERIPH_BASE + 0x3C00)
#define TIM15_BASE            (APB2PERIPH_BASE + 0x4000)
#define TIM16_BASE            (APB2PERIPH_BASE + 0x4400)
#define TIM17_BASE            (APB2PERIPH_BASE + 0x4800)
#define TIM9_BASE             (APB2PERIPH_BASE + 0x4C00)
#define TIM10_BASE            (APB2PERIPH_BASE + 0x5000)
#define TIM11_BASE            (APB2PERIPH_BASE + 0x5400)
#define SDIO_BASE             (APB2PERIPH_BASE + 0x8000)

#define DMA1_BASE             (AHBPERIPH_BASE + 0x0000)
#define DMA1_Channel1_BASE    (AHBPERIPH_BASE + 0x0008)
#define DMA1_Channel2_BASE    (AHBPERIPH_BASE + 0x001C)
#define DMA1_Channel3_BASE    (AHBPERIPH_BASE + 0x0030)
#define DMA1_Channel4_BASE    (AHBPERIPH_BASE + 0x0044)
#define DMA1_Channel5_BASE    (AHBPERIPH_BASE + 0x0058)
#define DMA1_Channel6_BASE    (AHBPERIPH_BASE + 0x006C)
#define DMA1_Channel7_BASE    (AHBPERIPH_BASE + 0x0080)
#define DMA2_BASE             (AHBPERIPH_BASE + 0x0400)
#define DMA2_Channel1_BASE    (AHBPERIPH_BASE + 0x0408)
#define DMA2_Channel2_BASE    (AHBPERIPH_BASE + 0x041C)
#define DMA2_Channel3_BASE    (AHBPERIPH_BASE + 0x0430)
#define DMA2_Channel4_BASE    (AHBPERIPH_BASE + 0x0444)
#define DMA2_Channel5_BASE    (AHBPERIPH_BASE + 0x0458)
#define DMA2_Channel6_BASE    (AHBPERIPH_BASE + 0x046C)
#define DMA2_Channel7_BASE    (AHBPERIPH_BASE + 0x0480)
#define DMA2_Channel8_BASE    (AHBPERIPH_BASE + 0x0490)
#define DMA2_Channel9_BASE    (AHBPERIPH_BASE + 0x04A0)
#define DMA2_Channel10_BASE   (AHBPERIPH_BASE + 0x04B0)
#define DMA2_Channel11_BASE   (AHBPERIPH_BASE + 0x04C0)
#define DMA2_EXTEN_BASE       (AHBPERIPH_BASE + 0x04D0)
#define RCC_BASE              (AHBPERIPH_BASE + 0x1000)
#define FLASH_R_BASE          (AHBPERIPH_BASE + 0x2000)
#define CRC_BASE              (AHBPERIPH_BASE + 0x3000)
#define USBHS_BASE            (AHBPERIPH_BASE + 0x3400)
#define EXTEN_BASE            (AHBPERIPH_BASE + 0x3800)
#define OPA_BASE              (AHBPERIPH_BASE + 0x3804)
#define RNG_BASE              (AHBPERIPH_BASE + 0x3C00)

#define ETH_BASE              (AHBPERIPH_BASE + 0x8000)
#define ETH_MAC_BASE          (ETH_BASE)
#define ETH_MMC_BASE          (ETH_BASE + 0x0100)
#define ETH_PTP_BASE          (ETH_BASE + 0x0700)
#define ETH_DMA_BASE          (ETH_BASE + 0x1000)

#define USBFS_BASE            ((uint32_t)0x50000000)
#define DVP_BASE              ((uint32_t)0x50050000)

#define FSMC_Bank1_R_BASE     (FSMC_R_BASE + 0x0000) 
#define FSMC_Bank1E_R_BASE    (FSMC_R_BASE + 0x0104) 
#define FSMC_Bank2_R_BASE     (FSMC_R_BASE + 0x0060) 

#define OB_BASE               ((uint32_t)0x1FFFF800)

/* Peripheral declaration */
#define TIM2                ((TIM_TypeDef *) TIM2_BASE)
#define TIM3                ((TIM_TypeDef *) TIM3_BASE)
#define TIM4                ((TIM_TypeDef *) TIM4_BASE)
#define TIM5                ((TIM_TypeDef *) TIM5_BASE)
#define TIM6                ((TIM_TypeDef *) TIM6_BASE)
#define TIM7                ((TIM_TypeDef *) TIM7_BASE)
#define UART6               ((USART_TypeDef *) UART6_BASE)
#define UART7               ((USART_TypeDef *) UART7_BASE)
#define UART8               ((USART_TypeDef *) UART8_BASE)
#define RTC                 ((RTC_TypeDef *) RTC_BASE)
#define WWDG                ((WWDG_TypeDef *) WWDG_BASE)
#define IWDG                ((IWDG_TypeDef *) IWDG_BASE)
#define SPI2                ((spi_s *) SPI2_BASE)
#define SPI3                ((spi_s *) SPI3_BASE)
#define USART2              ((USART_TypeDef *) USART2_BASE)
#define USART3              ((USART_TypeDef *) USART3_BASE)
#define UART4               ((USART_TypeDef *) UART4_BASE)
#define UART5               ((USART_TypeDef *) UART5_BASE)
#define I2C1                ((i2c_s *) I2C1_BASE)
#define I2C2                ((i2c_s *) I2C2_BASE)
#define CAN1                ((CAN_TypeDef *) CAN1_BASE)
#define CAN2                ((CAN_TypeDef *) CAN2_BASE)
#define BKP                 ((BKP_TypeDef *) BKP_BASE)
#define PWR                 ((PWR_TypeDef *) PWR_BASE)
#define DAC                 ((DAC_TypeDef *) DAC_BASE)

#define AFIO                ((AFIO_TypeDef *) AFIO_BASE)
#define EXTI                ((EXTI_TypeDef *) EXTI_BASE)
#define GPIOA               ((gpio_s *) GPIOA_BASE)
#define GPIOB               ((gpio_s *) GPIOB_BASE)
#define GPIOC               ((gpio_s *) GPIOC_BASE)
#define GPIOD               ((gpio_s *) GPIOD_BASE)
#define GPIOE               ((gpio_s *) GPIOE_BASE)
#define GPIOF               ((gpio_s *) GPIOF_BASE)
#define GPIOG               ((gpio_s *) GPIOG_BASE)
#define ADC1                ((ADC_TypeDef *) ADC1_BASE)
#define ADC2                ((ADC_TypeDef *) ADC2_BASE)
#define TKey1               ((ADC_TypeDef *) ADC1_BASE)
#define TKey2               ((ADC_TypeDef *) ADC2_BASE)
#define TIM1                ((TIM_TypeDef *) TIM1_BASE)
#define SPI1                ((spi_s *) SPI1_BASE)
#define TIM8                ((TIM_TypeDef *) TIM8_BASE)
#define USART1              ((USART_TypeDef *) USART1_BASE)
#define ADC3                ((ADC_TypeDef *) ADC3_BASE)
#define TIM15               ((TIM_TypeDef *) TIM15_BASE)
#define TIM16               ((TIM_TypeDef *) TIM16_BASE)
#define TIM17               ((TIM_TypeDef *) TIM17_BASE)
#define TIM9                ((TIM_TypeDef *) TIM9_BASE)
#define TIM10               ((TIM_TypeDef *) TIM10_BASE)
#define TIM11               ((TIM_TypeDef *) TIM11_BASE)
#define SDIO                ((SDIO_TypeDef *) SDIO_BASE)

#define DMA1                ((DMA_TypeDef *) DMA1_BASE)
#define DMA2                ((DMA_TypeDef *) DMA2_BASE)
#define DMA2_EXTEN          ((DMA_TypeDef *) DMA2_EXTEN_BASE)
#define DMA1_Channel1       ((DMA_Channel_TypeDef *) DMA1_Channel1_BASE)
#define DMA1_Channel2       ((DMA_Channel_TypeDef *) DMA1_Channel2_BASE)
#define DMA1_Channel3       ((DMA_Channel_TypeDef *) DMA1_Channel3_BASE)
#define DMA1_Channel4       ((DMA_Channel_TypeDef *) DMA1_Channel4_BASE)
#define DMA1_Channel5       ((DMA_Channel_TypeDef *) DMA1_Channel5_BASE)
#define DMA1_Channel6       ((DMA_Channel_TypeDef *) DMA1_Channel6_BASE)
#define DMA1_Channel7       ((DMA_Channel_TypeDef *) DMA1_Channel7_BASE)
#define DMA2_Channel1       ((DMA_Channel_TypeDef *) DMA2_Channel1_BASE)
#define DMA2_Channel2       ((DMA_Channel_TypeDef *) DMA2_Channel2_BASE)
#define DMA2_Channel3       ((DMA_Channel_TypeDef *) DMA2_Channel3_BASE)
#define DMA2_Channel4       ((DMA_Channel_TypeDef *) DMA2_Channel4_BASE)
#define DMA2_Channel5       ((DMA_Channel_TypeDef *) DMA2_Channel5_BASE)
#define DMA2_Channel6       ((DMA_Channel_TypeDef *) DMA2_Channel6_BASE)
#define DMA2_Channel7       ((DMA_Channel_TypeDef *) DMA2_Channel7_BASE)
#define DMA2_Channel8       ((DMA_Channel_TypeDef *) DMA2_Channel8_BASE)
#define DMA2_Channel9       ((DMA_Channel_TypeDef *) DMA2_Channel9_BASE)
#define DMA2_Channel10      ((DMA_Channel_TypeDef *) DMA2_Channel10_BASE)
#define DMA2_Channel11      ((DMA_Channel_TypeDef *) DMA2_Channel11_BASE)
#define RCC                 ((RCC_TypeDef *) RCC_BASE)
#define FLASH               ((FLASH_TypeDef *) FLASH_R_BASE)
#define CRC                 ((CRC_TypeDef *) CRC_BASE)
#define USBHSD              ((USBHSD_TypeDef *) USBHS_BASE)
#define USBHSH              ((USBHSH_TypeDef *) USBHS_BASE)
#define USBOTG_FS           ((USBOTG_FS_TypeDef *)USBFS_BASE)
#define USBOTG_H_FS         ((USBOTGH_FS_TypeDef *)USBFS_BASE)
#define EXTEN               ((EXTEN_TypeDef *) EXTEN_BASE)
#define OPA                 ((OPA_TypeDef *) OPA_BASE)
#define RNG                 ((RNG_TypeDef *) RNG_BASE)
#define ETH                 ((ETH_TypeDef *) ETH_BASE)

#define DVP                 ((DVP_TypeDef *) DVP_BASE)

#define FSMC_Bank1          ((FSMC_Bank1_TypeDef *) FSMC_Bank1_R_BASE)
#define FSMC_Bank1E         ((FSMC_Bank1E_TypeDef *) FSMC_Bank1E_R_BASE)
#define FSMC_Bank2          ((FSMC_Bank2_TypeDef *) FSMC_Bank2_R_BASE)

#define OB                  ((OB_TypeDef *) OB_BASE)

/******************************************************************************/
/*                         Peripheral Registers Bits Definition               */
/******************************************************************************/

/******************************************************************************/
/*                        Analog to Digital Converter                         */
/******************************************************************************/

/********************  Bit definition for ADC_STATR register  ********************/
#define  ADC_AWD                        ((uint8_t)0x01)               /* Analog watchdog flag */
#define  ADC_EOC                        ((uint8_t)0x02)               /* End of conversion */
#define  ADC_JEOC                       ((uint8_t)0x04)               /* Injected channel end of conversion */
#define  ADC_JSTRT                      ((uint8_t)0x08)               /* Injected channel Start flag */
#define  ADC_STRT                       ((uint8_t)0x10)               /* Regular channel Start flag */

/*******************  Bit definition for ADC_CTLR1 register  ********************/
#define  ADC_AWDCH                      ((uint32_t)0x0000001F)        /* AWDCH[4:0] bits (Analog watchdog channel select bits) */
#define  ADC_AWDCH_0                    ((uint32_t)0x00000001)        /* Bit 0 */
#define  ADC_AWDCH_1                    ((uint32_t)0x00000002)        /* Bit 1 */
#define  ADC_AWDCH_2                    ((uint32_t)0x00000004)        /* Bit 2 */
#define  ADC_AWDCH_3                    ((uint32_t)0x00000008)        /* Bit 3 */
#define  ADC_AWDCH_4                    ((uint32_t)0x00000010)        /* Bit 4 */

#define  ADC_EOCIE                      ((uint32_t)0x00000020)        /* Interrupt enable for EOC */
#define  ADC_AWDIE                      ((uint32_t)0x00000040)        /* Analog Watchdog interrupt enable */
#define  ADC_JEOCIE                     ((uint32_t)0x00000080)        /* Interrupt enable for injected channels */
#define  ADC_SCAN                       ((uint32_t)0x00000100)        /* Scan mode */
#define  ADC_AWDSGL                     ((uint32_t)0x00000200)        /* Enable the watchdog on a single channel in scan mode */
#define  ADC_JAUTO                      ((uint32_t)0x00000400)        /* Automatic injected group conversion */
#define  ADC_DISCEN                     ((uint32_t)0x00000800)        /* Discontinuous mode on regular channels */
#define  ADC_JDISCEN                    ((uint32_t)0x00001000)        /* Discontinuous mode on injected channels */

#define  ADC_DISCNUM                    ((uint32_t)0x0000E000)        /* DISCNUM[2:0] bits (Discontinuous mode channel count) */
#define  ADC_DISCNUM_0                  ((uint32_t)0x00002000)        /* Bit 0 */
#define  ADC_DISCNUM_1                  ((uint32_t)0x00004000)        /* Bit 1 */
#define  ADC_DISCNUM_2                  ((uint32_t)0x00008000)        /* Bit 2 */

#define  ADC_DUALMOD                    ((uint32_t)0x000F0000)        /* DUALMOD[3:0] bits (Dual mode selection) */
#define  ADC_DUALMOD_0                  ((uint32_t)0x00010000)        /* Bit 0 */
#define  ADC_DUALMOD_1                  ((uint32_t)0x00020000)        /* Bit 1 */
#define  ADC_DUALMOD_2                  ((uint32_t)0x00040000)        /* Bit 2 */
#define  ADC_DUALMOD_3                  ((uint32_t)0x00080000)        /* Bit 3 */

#define  ADC_JAWDEN                     ((uint32_t)0x00400000)        /* Analog watchdog enable on injected channels */
#define  ADC_AWDEN                      ((uint32_t)0x00800000)        /* Analog watchdog enable on regular channels */

/*******************  Bit definition for ADC_CTLR2 register  ********************/
#define  ADC_ADON                       ((uint32_t)0x00000001)        /* A/D Converter ON / OFF */
#define  ADC_CONT                       ((uint32_t)0x00000002)        /* Continuous Conversion */
#define  ADC_CAL                        ((uint32_t)0x00000004)        /* A/D Calibration */
#define  ADC_RSTCAL                     ((uint32_t)0x00000008)        /* Reset Calibration */
#define  ADC_DMA                        ((uint32_t)0x00000100)        /* Direct Memory access mode */
#define  ADC_ALIGN                      ((uint32_t)0x00000800)        /* Data Alignment */

#define  ADC_JEXTSEL                    ((uint32_t)0x00007000)        /* JEXTSEL[2:0] bits (External event select for injected group) */
#define  ADC_JEXTSEL_0                  ((uint32_t)0x00001000)        /* Bit 0 */
#define  ADC_JEXTSEL_1                  ((uint32_t)0x00002000)        /* Bit 1 */
#define  ADC_JEXTSEL_2                  ((uint32_t)0x00004000)        /* Bit 2 */

#define  ADC_JEXTTRIG                   ((uint32_t)0x00008000)        /* External Trigger Conversion mode for injected channels */

#define  ADC_EXTSEL                     ((uint32_t)0x000E0000)        /* EXTSEL[2:0] bits (External Event Select for regular group) */
#define  ADC_EXTSEL_0                   ((uint32_t)0x00020000)        /* Bit 0 */
#define  ADC_EXTSEL_1                   ((uint32_t)0x00040000)        /* Bit 1 */
#define  ADC_EXTSEL_2                   ((uint32_t)0x00080000)        /* Bit 2 */

#define  ADC_EXTTRIG                    ((uint32_t)0x00100000)        /* External Trigger Conversion mode for regular channels */
#define  ADC_JSWSTART                   ((uint32_t)0x00200000)        /* Start Conversion of injected channels */
#define  ADC_SWSTART                    ((uint32_t)0x00400000)        /* Start Conversion of regular channels */
#define  ADC_TSVREFE                    ((uint32_t)0x00800000)        /* Temperature Sensor and VREFINT Enable */

/******************  Bit definition for ADC_SAMPTR1 register  *******************/
#define  ADC_SMP10                      ((uint32_t)0x00000007)        /* SMP10[2:0] bits (Channel 10 Sample time selection) */
#define  ADC_SMP10_0                    ((uint32_t)0x00000001)        /* Bit 0 */
#define  ADC_SMP10_1                    ((uint32_t)0x00000002)        /* Bit 1 */
#define  ADC_SMP10_2                    ((uint32_t)0x00000004)        /* Bit 2 */

#define  ADC_SMP11                      ((uint32_t)0x00000038)        /* SMP11[2:0] bits (Channel 11 Sample time selection) */
#define  ADC_SMP11_0                    ((uint32_t)0x00000008)        /* Bit 0 */
#define  ADC_SMP11_1                    ((uint32_t)0x00000010)        /* Bit 1 */
#define  ADC_SMP11_2                    ((uint32_t)0x00000020)        /* Bit 2 */

#define  ADC_SMP12                      ((uint32_t)0x000001C0)        /* SMP12[2:0] bits (Channel 12 Sample time selection) */
#define  ADC_SMP12_0                    ((uint32_t)0x00000040)        /* Bit 0 */
#define  ADC_SMP12_1                    ((uint32_t)0x00000080)        /* Bit 1 */
#define  ADC_SMP12_2                    ((uint32_t)0x00000100)        /* Bit 2 */

#define  ADC_SMP13                      ((uint32_t)0x00000E00)        /* SMP13[2:0] bits (Channel 13 Sample time selection) */
#define  ADC_SMP13_0                    ((uint32_t)0x00000200)        /* Bit 0 */
#define  ADC_SMP13_1                    ((uint32_t)0x00000400)        /* Bit 1 */
#define  ADC_SMP13_2                    ((uint32_t)0x00000800)        /* Bit 2 */

#define  ADC_SMP14                      ((uint32_t)0x00007000)        /* SMP14[2:0] bits (Channel 14 Sample time selection) */
#define  ADC_SMP14_0                    ((uint32_t)0x00001000)        /* Bit 0 */
#define  ADC_SMP14_1                    ((uint32_t)0x00002000)        /* Bit 1 */
#define  ADC_SMP14_2                    ((uint32_t)0x00004000)        /* Bit 2 */

#define  ADC_SMP15                      ((uint32_t)0x00038000)        /* SMP15[2:0] bits (Channel 15 Sample time selection) */
#define  ADC_SMP15_0                    ((uint32_t)0x00008000)        /* Bit 0 */
#define  ADC_SMP15_1                    ((uint32_t)0x00010000)        /* Bit 1 */
#define  ADC_SMP15_2                    ((uint32_t)0x00020000)        /* Bit 2 */

#define  ADC_SMP16                      ((uint32_t)0x001C0000)        /* SMP16[2:0] bits (Channel 16 Sample time selection) */
#define  ADC_SMP16_0                    ((uint32_t)0x00040000)        /* Bit 0 */
#define  ADC_SMP16_1                    ((uint32_t)0x00080000)        /* Bit 1 */
#define  ADC_SMP16_2                    ((uint32_t)0x00100000)        /* Bit 2 */

#define  ADC_SMP17                      ((uint32_t)0x00E00000)        /* SMP17[2:0] bits (Channel 17 Sample time selection) */
#define  ADC_SMP17_0                    ((uint32_t)0x00200000)        /* Bit 0 */
#define  ADC_SMP17_1                    ((uint32_t)0x00400000)        /* Bit 1 */
#define  ADC_SMP17_2                    ((uint32_t)0x00800000)        /* Bit 2 */

/******************  Bit definition for ADC_SAMPTR2 register  *******************/
#define  ADC_SMP0                       ((uint32_t)0x00000007)        /* SMP0[2:0] bits (Channel 0 Sample time selection) */
#define  ADC_SMP0_0                     ((uint32_t)0x00000001)        /* Bit 0 */
#define  ADC_SMP0_1                     ((uint32_t)0x00000002)        /* Bit 1 */
#define  ADC_SMP0_2                     ((uint32_t)0x00000004)        /* Bit 2 */

#define  ADC_SMP1                       ((uint32_t)0x00000038)        /* SMP1[2:0] bits (Channel 1 Sample time selection) */
#define  ADC_SMP1_0                     ((uint32_t)0x00000008)        /* Bit 0 */
#define  ADC_SMP1_1                     ((uint32_t)0x00000010)        /* Bit 1 */
#define  ADC_SMP1_2                     ((uint32_t)0x00000020)        /* Bit 2 */

#define  ADC_SMP2                       ((uint32_t)0x000001C0)        /* SMP2[2:0] bits (Channel 2 Sample time selection) */
#define  ADC_SMP2_0                     ((uint32_t)0x00000040)        /* Bit 0 */
#define  ADC_SMP2_1                     ((uint32_t)0x00000080)        /* Bit 1 */
#define  ADC_SMP2_2                     ((uint32_t)0x00000100)        /* Bit 2 */

#define  ADC_SMP3                       ((uint32_t)0x00000E00)        /* SMP3[2:0] bits (Channel 3 Sample time selection) */
#define  ADC_SMP3_0                     ((uint32_t)0x00000200)        /* Bit 0 */
#define  ADC_SMP3_1                     ((uint32_t)0x00000400)        /* Bit 1 */
#define  ADC_SMP3_2                     ((uint32_t)0x00000800)        /* Bit 2 */

#define  ADC_SMP4                       ((uint32_t)0x00007000)        /* SMP4[2:0] bits (Channel 4 Sample time selection) */
#define  ADC_SMP4_0                     ((uint32_t)0x00001000)        /* Bit 0 */
#define  ADC_SMP4_1                     ((uint32_t)0x00002000)        /* Bit 1 */
#define  ADC_SMP4_2                     ((uint32_t)0x00004000)        /* Bit 2 */

#define  ADC_SMP5                       ((uint32_t)0x00038000)        /* SMP5[2:0] bits (Channel 5 Sample time selection) */
#define  ADC_SMP5_0                     ((uint32_t)0x00008000)        /* Bit 0 */
#define  ADC_SMP5_1                     ((uint32_t)0x00010000)        /* Bit 1 */
#define  ADC_SMP5_2                     ((uint32_t)0x00020000)        /* Bit 2 */

#define  ADC_SMP6                       ((uint32_t)0x001C0000)        /* SMP6[2:0] bits (Channel 6 Sample time selection) */
#define  ADC_SMP6_0                     ((uint32_t)0x00040000)        /* Bit 0 */
#define  ADC_SMP6_1                     ((uint32_t)0x00080000)        /* Bit 1 */
#define  ADC_SMP6_2                     ((uint32_t)0x00100000)        /* Bit 2 */

#define  ADC_SMP7                       ((uint32_t)0x00E00000)        /* SMP7[2:0] bits (Channel 7 Sample time selection) */
#define  ADC_SMP7_0                     ((uint32_t)0x00200000)        /* Bit 0 */
#define  ADC_SMP7_1                     ((uint32_t)0x00400000)        /* Bit 1 */
#define  ADC_SMP7_2                     ((uint32_t)0x00800000)        /* Bit 2 */

#define  ADC_SMP8                       ((uint32_t)0x07000000)        /* SMP8[2:0] bits (Channel 8 Sample time selection) */
#define  ADC_SMP8_0                     ((uint32_t)0x01000000)        /* Bit 0 */
#define  ADC_SMP8_1                     ((uint32_t)0x02000000)        /* Bit 1 */
#define  ADC_SMP8_2                     ((uint32_t)0x04000000)        /* Bit 2 */

#define  ADC_SMP9                       ((uint32_t)0x38000000)        /* SMP9[2:0] bits (Channel 9 Sample time selection) */
#define  ADC_SMP9_0                     ((uint32_t)0x08000000)        /* Bit 0 */
#define  ADC_SMP9_1                     ((uint32_t)0x10000000)        /* Bit 1 */
#define  ADC_SMP9_2                     ((uint32_t)0x20000000)        /* Bit 2 */

/******************  Bit definition for ADC_IOFR1 register  *******************/
#define  ADC_JOFFSET1                   ((uint16_t)0x0FFF)            /* Data offset for injected channel 1 */

/******************  Bit definition for ADC_IOFR2 register  *******************/
#define  ADC_JOFFSET2                   ((uint16_t)0x0FFF)            /* Data offset for injected channel 2 */

/******************  Bit definition for ADC_IOFR3 register  *******************/
#define  ADC_JOFFSET3                   ((uint16_t)0x0FFF)            /* Data offset for injected channel 3 */

/******************  Bit definition for ADC_IOFR4 register  *******************/
#define  ADC_JOFFSET4                   ((uint16_t)0x0FFF)            /* Data offset for injected channel 4 */

/*******************  Bit definition for ADC_WDHTR register  ********************/
#define  ADC_HT                         ((uint16_t)0x0FFF)            /* Analog watchdog high threshold */

/*******************  Bit definition for ADC_WDLTR register  ********************/
#define  ADC_LT                         ((uint16_t)0x0FFF)            /* Analog watchdog low threshold */

/*******************  Bit definition for ADC_RSQR1 register  *******************/
#define  ADC_SQ13                       ((uint32_t)0x0000001F)        /* SQ13[4:0] bits (13th conversion in regular sequence) */
#define  ADC_SQ13_0                     ((uint32_t)0x00000001)        /* Bit 0 */
#define  ADC_SQ13_1                     ((uint32_t)0x00000002)        /* Bit 1 */
#define  ADC_SQ13_2                     ((uint32_t)0x00000004)        /* Bit 2 */
#define  ADC_SQ13_3                     ((uint32_t)0x00000008)        /* Bit 3 */
#define  ADC_SQ13_4                     ((uint32_t)0x00000010)        /* Bit 4 */

#define  ADC_SQ14                       ((uint32_t)0x000003E0)        /* SQ14[4:0] bits (14th conversion in regular sequence) */
#define  ADC_SQ14_0                     ((uint32_t)0x00000020)        /* Bit 0 */
#define  ADC_SQ14_1                     ((uint32_t)0x00000040)        /* Bit 1 */
#define  ADC_SQ14_2                     ((uint32_t)0x00000080)        /* Bit 2 */
#define  ADC_SQ14_3                     ((uint32_t)0x00000100)        /* Bit 3 */
#define  ADC_SQ14_4                     ((uint32_t)0x00000200)        /* Bit 4 */

#define  ADC_SQ15                       ((uint32_t)0x00007C00)        /* SQ15[4:0] bits (15th conversion in regular sequence) */
#define  ADC_SQ15_0                     ((uint32_t)0x00000400)        /* Bit 0 */
#define  ADC_SQ15_1                     ((uint32_t)0x00000800)        /* Bit 1 */
#define  ADC_SQ15_2                     ((uint32_t)0x00001000)        /* Bit 2 */
#define  ADC_SQ15_3                     ((uint32_t)0x00002000)        /* Bit 3 */
#define  ADC_SQ15_4                     ((uint32_t)0x00004000)        /* Bit 4 */

#define  ADC_SQ16                       ((uint32_t)0x000F8000)        /* SQ16[4:0] bits (16th conversion in regular sequence) */
#define  ADC_SQ16_0                     ((uint32_t)0x00008000)        /* Bit 0 */
#define  ADC_SQ16_1                     ((uint32_t)0x00010000)        /* Bit 1 */
#define  ADC_SQ16_2                     ((uint32_t)0x00020000)        /* Bit 2 */
#define  ADC_SQ16_3                     ((uint32_t)0x00040000)        /* Bit 3 */
#define  ADC_SQ16_4                     ((uint32_t)0x00080000)        /* Bit 4 */

#define  ADC_L                          ((uint32_t)0x00F00000)        /* L[3:0] bits (Regular channel sequence length) */
#define  ADC_L_0                        ((uint32_t)0x00100000)        /* Bit 0 */
#define  ADC_L_1                        ((uint32_t)0x00200000)        /* Bit 1 */
#define  ADC_L_2                        ((uint32_t)0x00400000)        /* Bit 2 */
#define  ADC_L_3                        ((uint32_t)0x00800000)        /* Bit 3 */

/*******************  Bit definition for ADC_RSQR2 register  *******************/
#define  ADC_SQ7                        ((uint32_t)0x0000001F)        /* SQ7[4:0] bits (7th conversion in regular sequence) */
#define  ADC_SQ7_0                      ((uint32_t)0x00000001)        /* Bit 0 */
#define  ADC_SQ7_1                      ((uint32_t)0x00000002)        /* Bit 1 */
#define  ADC_SQ7_2                      ((uint32_t)0x00000004)        /* Bit 2 */
#define  ADC_SQ7_3                      ((uint32_t)0x00000008)        /* Bit 3 */
#define  ADC_SQ7_4                      ((uint32_t)0x00000010)        /* Bit 4 */

#define  ADC_SQ8                        ((uint32_t)0x000003E0)        /* SQ8[4:0] bits (8th conversion in regular sequence) */
#define  ADC_SQ8_0                      ((uint32_t)0x00000020)        /* Bit 0 */
#define  ADC_SQ8_1                      ((uint32_t)0x00000040)        /* Bit 1 */
#define  ADC_SQ8_2                      ((uint32_t)0x00000080)        /* Bit 2 */
#define  ADC_SQ8_3                      ((uint32_t)0x00000100)        /* Bit 3 */
#define  ADC_SQ8_4                      ((uint32_t)0x00000200)        /* Bit 4 */

#define  ADC_SQ9                        ((uint32_t)0x00007C00)        /* SQ9[4:0] bits (9th conversion in regular sequence) */
#define  ADC_SQ9_0                      ((uint32_t)0x00000400)        /* Bit 0 */
#define  ADC_SQ9_1                      ((uint32_t)0x00000800)        /* Bit 1 */
#define  ADC_SQ9_2                      ((uint32_t)0x00001000)        /* Bit 2 */
#define  ADC_SQ9_3                      ((uint32_t)0x00002000)        /* Bit 3 */
#define  ADC_SQ9_4                      ((uint32_t)0x00004000)        /* Bit 4 */

#define  ADC_SQ10                       ((uint32_t)0x000F8000)        /* SQ10[4:0] bits (10th conversion in regular sequence) */
#define  ADC_SQ10_0                     ((uint32_t)0x00008000)        /* Bit 0 */
#define  ADC_SQ10_1                     ((uint32_t)0x00010000)        /* Bit 1 */
#define  ADC_SQ10_2                     ((uint32_t)0x00020000)        /* Bit 2 */
#define  ADC_SQ10_3                     ((uint32_t)0x00040000)        /* Bit 3 */
#define  ADC_SQ10_4                     ((uint32_t)0x00080000)        /* Bit 4 */

#define  ADC_SQ11                       ((uint32_t)0x01F00000)        /* SQ11[4:0] bits (11th conversion in regular sequence) */
#define  ADC_SQ11_0                     ((uint32_t)0x00100000)        /* Bit 0 */
#define  ADC_SQ11_1                     ((uint32_t)0x00200000)        /* Bit 1 */
#define  ADC_SQ11_2                     ((uint32_t)0x00400000)        /* Bit 2 */
#define  ADC_SQ11_3                     ((uint32_t)0x00800000)        /* Bit 3 */
#define  ADC_SQ11_4                     ((uint32_t)0x01000000)        /* Bit 4 */

#define  ADC_SQ12                       ((uint32_t)0x3E000000)        /* SQ12[4:0] bits (12th conversion in regular sequence) */
#define  ADC_SQ12_0                     ((uint32_t)0x02000000)        /* Bit 0 */
#define  ADC_SQ12_1                     ((uint32_t)0x04000000)        /* Bit 1 */
#define  ADC_SQ12_2                     ((uint32_t)0x08000000)        /* Bit 2 */
#define  ADC_SQ12_3                     ((uint32_t)0x10000000)        /* Bit 3 */
#define  ADC_SQ12_4                     ((uint32_t)0x20000000)        /* Bit 4 */

/*******************  Bit definition for ADC_RSQR3 register  *******************/
#define  ADC_SQ1                        ((uint32_t)0x0000001F)        /* SQ1[4:0] bits (1st conversion in regular sequence) */
#define  ADC_SQ1_0                      ((uint32_t)0x00000001)        /* Bit 0 */
#define  ADC_SQ1_1                      ((uint32_t)0x00000002)        /* Bit 1 */
#define  ADC_SQ1_2                      ((uint32_t)0x00000004)        /* Bit 2 */
#define  ADC_SQ1_3                      ((uint32_t)0x00000008)        /* Bit 3 */
#define  ADC_SQ1_4                      ((uint32_t)0x00000010)        /* Bit 4 */

#define  ADC_SQ2                        ((uint32_t)0x000003E0)        /* SQ2[4:0] bits (2nd conversion in regular sequence) */
#define  ADC_SQ2_0                      ((uint32_t)0x00000020)        /* Bit 0 */
#define  ADC_SQ2_1                      ((uint32_t)0x00000040)        /* Bit 1 */
#define  ADC_SQ2_2                      ((uint32_t)0x00000080)        /* Bit 2 */
#define  ADC_SQ2_3                      ((uint32_t)0x00000100)        /* Bit 3 */
#define  ADC_SQ2_4                      ((uint32_t)0x00000200)        /* Bit 4 */

#define  ADC_SQ3                        ((uint32_t)0x00007C00)        /* SQ3[4:0] bits (3rd conversion in regular sequence) */
#define  ADC_SQ3_0                      ((uint32_t)0x00000400)        /* Bit 0 */
#define  ADC_SQ3_1                      ((uint32_t)0x00000800)        /* Bit 1 */
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
#define  ADC_JSQ4_2                     ((uint32_t)0x00020000)        /* Bit 2 */
#define  ADC_JSQ4_3                     ((uint32_t)0x00040000)        /* Bit 3 */
#define  ADC_JSQ4_4                     ((uint32_t)0x00080000)        /* Bit 4 */

#define  ADC_JL                         ((uint32_t)0x00300000)        /* JL[1:0] bits (Injected Sequence length) */
#define  ADC_JL_0                       ((uint32_t)0x00100000)        /* Bit 0 */
#define  ADC_JL_1                       ((uint32_t)0x00200000)        /* Bit 1 */

/*******************  Bit definition for ADC_IDATAR1 register  *******************/
#define  ADC_IDATAR1_JDATA              ((uint16_t)0xFFFF)            /* Injected data */

/*******************  Bit definition for ADC_IDATAR2 register  *******************/
#define  ADC_IDATAR2_JDATA              ((uint16_t)0xFFFF)            /* Injected data */

/*******************  Bit definition for ADC_IDATAR3 register  *******************/
#define  ADC_IDATAR3_JDATA              ((uint16_t)0xFFFF)            /* Injected data */

/*******************  Bit definition for ADC_IDATAR4 register  *******************/
#define  ADC_IDATAR4_JDATA              ((uint16_t)0xFFFF)            /* Injected data */

/********************  Bit definition for ADC_RDATAR register  ********************/
#define  ADC_RDATAR_DATA                ((uint32_t)0x0000FFFF)        /* Regular data */
#define  ADC_RDATAR_ADC2DATA            ((uint32_t)0xFFFF0000)        /* ADC2 data */

/******************************************************************************/
/*                            Backup registers                                */
/******************************************************************************/

/*******************  Bit definition for BKP_DATAR1 register  ********************/
#define  BKP_DATAR1_D                           ((uint16_t)0xFFFF)     /* Backup data */

/*******************  Bit definition for BKP_DATAR2 register  ********************/
#define  BKP_DATAR2_D                           ((uint16_t)0xFFFF)     /* Backup data */

/*******************  Bit definition for BKP_DATAR3 register  ********************/
#define  BKP_DATAR3_D                           ((uint16_t)0xFFFF)     /* Backup data */

/*******************  Bit definition for BKP_DATAR4 register  ********************/
#define  BKP_DATAR4_D                           ((uint16_t)0xFFFF)     /* Backup data */

/*******************  Bit definition for BKP_DATAR5 register  ********************/
#define  BKP_DATAR5_D                           ((uint16_t)0xFFFF)     /* Backup data */

/*******************  Bit definition for BKP_DATAR6 register  ********************/
#define  BKP_DATAR6_D                           ((uint16_t)0xFFFF)     /* Backup data */

/*******************  Bit definition for BKP_DATAR7 register  ********************/
#define  BKP_DATAR7_D                           ((uint16_t)0xFFFF)     /* Backup data */

/*******************  Bit definition for BKP_DATAR8 register  ********************/
#define  BKP_DATAR8_D                           ((uint16_t)0xFFFF)     /* Backup data */

/*******************  Bit definition for BKP_DATAR9 register  ********************/
#define  BKP_DATAR9_D                           ((uint16_t)0xFFFF)     /* Backup data */

/*******************  Bit definition for BKP_DATAR10 register  *******************/
#define  BKP_DATAR10_D                          ((uint16_t)0xFFFF)     /* Backup data */

/*******************  Bit definition for BKP_DATAR11 register  *******************/
#define  BKP_DATAR11_D                          ((uint16_t)0xFFFF)     /* Backup data */

/*******************  Bit definition for BKP_DATAR12 register  *******************/
#define  BKP_DATAR12_D                          ((uint16_t)0xFFFF)     /* Backup data */

/*******************  Bit definition for BKP_DATAR13 register  *******************/
#define  BKP_DATAR13_D                          ((uint16_t)0xFFFF)     /* Backup data */

/*******************  Bit definition for BKP_DATAR14 register  *******************/
#define  BKP_DATAR14_D                          ((uint16_t)0xFFFF)     /* Backup data */

/*******************  Bit definition for BKP_DATAR15 register  *******************/
#define  BKP_DATAR15_D                          ((uint16_t)0xFFFF)     /* Backup data */

/*******************  Bit definition for BKP_DATAR16 register  *******************/
#define  BKP_DATAR16_D                          ((uint16_t)0xFFFF)     /* Backup data */

/*******************  Bit definition for BKP_DATAR17 register  *******************/
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
#define  BKP_DATAR41_D                          ((uint16_t)0xFFFF)     /* Backup data */

/*******************  Bit definition for BKP_DATAR42 register  *******************/
#define  BKP_DATAR42_D                          ((uint16_t)0xFFFF)     /* Backup data */

/******************  Bit definition for BKP_OCTLR register  *******************/
#define  BKP_CAL                                ((uint16_t)0x007F)     /* Calibration value */
#define  BKP_CCO                                ((uint16_t)0x0080)     /* Calibration Clock Output */
#define  BKP_ASOE                               ((uint16_t)0x0100)     /* Alarm or Second Output Enable */
#define  BKP_ASOS                               ((uint16_t)0x0200)     /* Alarm or Second Output Selection */

/********************  Bit definition for BKP_TPCTLR register  ********************/
#define  BKP_TPE                                ((uint8_t)0x01)        /* TAMPER pin enable */
#define  BKP_TPAL                               ((uint8_t)0x02)        /* TAMPER pin active level */

/*******************  Bit definition for BKP_TPCSR register  ********************/
#define  BKP_CTE                                ((uint16_t)0x0001)     /* Clear Tamper event */
#define  BKP_CTI                                ((uint16_t)0x0002)     /* Clear Tamper Interrupt */
#define  BKP_TPIE                               ((uint16_t)0x0004)     /* TAMPER Pin interrupt enable */
#define  BKP_TEF                                ((uint16_t)0x0100)     /* Tamper Event Flag */
#define  BKP_TIF                                ((uint16_t)0x0200)     /* Tamper Interrupt Flag */

/******************************************************************************/
/*                         Controller Area Network                            */
/******************************************************************************/

/*******************  Bit definition for CAN_CTLR register  ********************/
#define  CAN_CTLR_INRQ                       ((uint16_t)0x0001)            /* Initialization Request */
#define  CAN_CTLR_SLEEP                      ((uint16_t)0x0002)            /* Sleep Mode Request */
#define  CAN_CTLR_TXFP                       ((uint16_t)0x0004)            /* Transmit FIFO Priority */
#define  CAN_CTLR_RFLM                       ((uint16_t)0x0008)            /* Receive FIFO Locked Mode */
#define  CAN_CTLR_NART                       ((uint16_t)0x0010)            /* No Automatic Retransmission */
#define  CAN_CTLR_AWUM                       ((uint16_t)0x0020)            /* Automatic Wakeup Mode */
#define  CAN_CTLR_ABOM                       ((uint16_t)0x0040)            /* Automatic Bus-Off Management */
#define  CAN_CTLR_TTCM                       ((uint16_t)0x0080)            /* Time Triggered Communication Mode */
#define  CAN_CTLR_RESET                      ((uint16_t)0x8000)            /* CAN software master reset */

/*******************  Bit definition for CAN_STATR register  ********************/
#define  CAN_STATR_INAK                      ((uint16_t)0x0001)            /* Initialization Acknowledge */
#define  CAN_STATR_SLAK                      ((uint16_t)0x0002)            /* Sleep Acknowledge */
#define  CAN_STATR_ERRI                      ((uint16_t)0x0004)            /* Error Interrupt */
#define  CAN_STATR_WKUI                      ((uint16_t)0x0008)            /* Wakeup Interrupt */
#define  CAN_STATR_SLAKI                     ((uint16_t)0x0010)            /* Sleep Acknowledge Interrupt */
#define  CAN_STATR_TXM                       ((uint16_t)0x0100)            /* Transmit Mode */
#define  CAN_STATR_RXM                       ((uint16_t)0x0200)            /* Receive Mode */
#define  CAN_STATR_SAMP                      ((uint16_t)0x0400)            /* Last Sample Point */
#define  CAN_STATR_RX                        ((uint16_t)0x0800)            /* CAN Rx Signal */

/*******************  Bit definition for CAN_TSTATR register  ********************/
#define  CAN_TSTATR_RQCP0                    ((uint32_t)0x00000001)        /* Request Completed Mailbox0 */
#define  CAN_TSTATR_TXOK0                    ((uint32_t)0x00000002)        /* Transmission OK of Mailbox0 */
#define  CAN_TSTATR_ALST0                    ((uint32_t)0x00000004)        /* Arbitration Lost for Mailbox0 */
#define  CAN_TSTATR_TERR0                    ((uint32_t)0x00000008)        /* Transmission Error of Mailbox0 */
#define  CAN_TSTATR_ABRQ0                    ((uint32_t)0x00000080)        /* Abort Request for Mailbox0 */
#define  CAN_TSTATR_RQCP1                    ((uint32_t)0x00000100)        /* Request Completed Mailbox1 */
#define  CAN_TSTATR_TXOK1                    ((uint32_t)0x00000200)        /* Transmission OK of Mailbox1 */
#define  CAN_TSTATR_ALST1                    ((uint32_t)0x00000400)        /* Arbitration Lost for Mailbox1 */
#define  CAN_TSTATR_TERR1                    ((uint32_t)0x00000800)        /* Transmission Error of Mailbox1 */
#define  CAN_TSTATR_ABRQ1                    ((uint32_t)0x00008000)        /* Abort Request for Mailbox 1 */
#define  CAN_TSTATR_RQCP2                    ((uint32_t)0x00010000)        /* Request Completed Mailbox2 */
#define  CAN_TSTATR_TXOK2                    ((uint32_t)0x00020000)        /* Transmission OK of Mailbox 2 */
#define  CAN_TSTATR_ALST2                    ((uint32_t)0x00040000)        /* Arbitration Lost for mailbox 2 */
#define  CAN_TSTATR_TERR2                    ((uint32_t)0x00080000)        /* Transmission Error of Mailbox 2 */
#define  CAN_TSTATR_ABRQ2                    ((uint32_t)0x00800000)        /* Abort Request for Mailbox 2 */
#define  CAN_TSTATR_CODE                     ((uint32_t)0x03000000)        /* Mailbox Code */

#define  CAN_TSTATR_TME                      ((uint32_t)0x1C000000)        /* TME[2:0] bits */
#define  CAN_TSTATR_TME0                     ((uint32_t)0x04000000)        /* Transmit Mailbox 0 Empty */
#define  CAN_TSTATR_TME1                     ((uint32_t)0x08000000)        /* Transmit Mailbox 1 Empty */
#define  CAN_TSTATR_TME2                     ((uint32_t)0x10000000)        /* Transmit Mailbox 2 Empty */

#define  CAN_TSTATR_LOW                      ((uint32_t)0xE0000000)        /* LOW[2:0] bits */
#define  CAN_TSTATR_LOW0                     ((uint32_t)0x20000000)        /* Lowest Priority Flag for Mailbox 0 */
#define  CAN_TSTATR_LOW1                     ((uint32_t)0x40000000)        /* Lowest Priority Flag for Mailbox 1 */
#define  CAN_TSTATR_LOW2                     ((uint32_t)0x80000000)        /* Lowest Priority Flag for Mailbox 2 */

/*******************  Bit definition for CAN_RFIFO0 register  *******************/
#define  CAN_RFIFO0_FMP0                     ((uint8_t)0x03)               /* FIFO 0 Message Pending */
#define  CAN_RFIFO0_FULL0                    ((uint8_t)0x08)               /* FIFO 0 Full */
#define  CAN_RFIFO0_FOVR0                    ((uint8_t)0x10)               /* FIFO 0 Overrun */
#define  CAN_RFIFO0_RFOM0                    ((uint8_t)0x20)               /* Release FIFO 0 Output Mailbox */

/*******************  Bit definition for CAN_RFIFO1 register  *******************/
#define  CAN_RFIFO1_FMP1                     ((uint8_t)0x03)               /* FIFO 1 Message Pending */
#define  CAN_RFIFO1_FULL1                    ((uint8_t)0x08)               /* FIFO 1 Full */
#define  CAN_RFIFO1_FOVR1                    ((uint8_t)0x10)               /* FIFO 1 Overrun */
#define  CAN_RFIFO1_RFOM1                    ((uint8_t)0x20)               /* Release FIFO 1 Output Mailbox */

/********************  Bit definition for CAN_INTENR register  *******************/
#define  CAN_INTENR_TMEIE                    ((uint32_t)0x00000001)        /* Transmit Mailbox Empty Interrupt Enable */
#define  CAN_INTENR_FMPIE0                   ((uint32_t)0x00000002)        /* FIFO Message Pending Interrupt Enable */
#define  CAN_INTENR_FFIE0                    ((uint32_t)0x00000004)        /* FIFO Full Interrupt Enable */
#define  CAN_INTENR_FOVIE0                   ((uint32_t)0x00000008)        /* FIFO Overrun Interrupt Enable */
#define  CAN_INTENR_FMPIE1                   ((uint32_t)0x00000010)        /* FIFO Message Pending Interrupt Enable */
#define  CAN_INTENR_FFIE1                    ((uint32_t)0x00000020)        /* FIFO Full Interrupt Enable */
#define  CAN_INTENR_FOVIE1                   ((uint32_t)0x00000040)        /* FIFO Overrun Interrupt Enable */
#define  CAN_INTENR_EWGIE                    ((uint32_t)0x00000100)        /* Error Warning Interrupt Enable */
#define  CAN_INTENR_EPVIE                    ((uint32_t)0x00000200)        /* Error Passive Interrupt Enable */
#define  CAN_INTENR_BOFIE                    ((uint32_t)0x00000400)        /* Bus-Off Interrupt Enable */
#define  CAN_INTENR_LECIE                    ((uint32_t)0x00000800)        /* Last Error Code Interrupt Enable */
#define  CAN_INTENR_ERRIE                    ((uint32_t)0x00008000)        /* Error Interrupt Enable */
#define  CAN_INTENR_WKUIE                    ((uint32_t)0x00010000)        /* Wakeup Interrupt Enable */
#define  CAN_INTENR_SLKIE                    ((uint32_t)0x00020000)        /* Sleep Interrupt Enable */

/********************  Bit definition for CAN_ERRSR register  *******************/
#define  CAN_ERRSR_EWGF                      ((uint32_t)0x00000001)        /* Error Warning Flag */
#define  CAN_ERRSR_EPVF                      ((uint32_t)0x00000002)        /* Error Passive Flag */
#define  CAN_ERRSR_BOFF                      ((uint32_t)0x00000004)        /* Bus-Off Flag */

#define  CAN_ERRSR_LEC                       ((uint32_t)0x00000070)        /* LEC[2:0] bits (Last Error Code) */
#define  CAN_ERRSR_LEC_0                     ((uint32_t)0x00000010)        /* Bit 0 */
#define  CAN_ERRSR_LEC_1                     ((uint32_t)0x00000020)        /* Bit 1 */
#define  CAN_ERRSR_LEC_2                     ((uint32_t)0x00000040)        /* Bit 2 */

#define  CAN_ERRSR_TEC                       ((uint32_t)0x00FF0000)        /* Least significant byte of the 9-bit Transmit Error Counter */
#define  CAN_ERRSR_REC                       ((uint32_t)0xFF000000)        /* Receive Error Counter */

/*******************  Bit definition for CAN_BTIMR register  ********************/
#define  CAN_BTIMR_BRP                       ((uint32_t)0x000003FF)        /* Baud Rate Prescaler */
#define  CAN_BTIMR_TS1                       ((uint32_t)0x000F0000)        /* Time Segment 1 */
#define  CAN_BTIMR_TS2                       ((uint32_t)0x00700000)        /* Time Segment 2 */
#define  CAN_BTIMR_SJW                       ((uint32_t)0x03000000)        /* Resynchronization Jump Width */
#define  CAN_BTIMR_LBKM                      ((uint32_t)0x40000000)        /* Loop Back Mode (Debug) */
#define  CAN_BTIMR_SILM                      ((uint32_t)0x80000000)        /* Silent Mode */

/******************  Bit definition for CAN_TXMI0R register  ********************/
#define  CAN_TXMI0R_TXRQ                     ((uint32_t)0x00000001)        /* Transmit Mailbox Request */
#define  CAN_TXMI0R_RTR                      ((uint32_t)0x00000002)        /* Remote Transmission Request */
#define  CAN_TXMI0R_IDE                      ((uint32_t)0x00000004)        /* Identifier Extension */
#define  CAN_TXMI0R_EXID                     ((uint32_t)0x001FFFF8)        /* Extended Identifier */
#define  CAN_TXMI0R_STID                     ((uint32_t)0xFFE00000)        /* Standard Identifier or Extended Identifier */

/******************  Bit definition for CAN_TXMDT0R register  *******************/
#define  CAN_TXMDT0R_DLC                     ((uint32_t)0x0000000F)        /* Data Length Code */
#define  CAN_TXMDT0R_TGT                     ((uint32_t)0x00000100)        /* Transmit Global Time */
#define  CAN_TXMDT0R_TIME                    ((uint32_t)0xFFFF0000)        /* Message Time Stamp */

/******************  Bit definition for CAN_TXMDL0R register  *******************/
#define  CAN_TXMDL0R_DATA0                   ((uint32_t)0x000000FF)        /* Data byte 0 */
#define  CAN_TXMDL0R_DATA1                   ((uint32_t)0x0000FF00)        /* Data byte 1 */
#define  CAN_TXMDL0R_DATA2                   ((uint32_t)0x00FF0000)        /* Data byte 2 */
#define  CAN_TXMDL0R_DATA3                   ((uint32_t)0xFF000000)        /* Data byte 3 */

/******************  Bit definition for CAN_TXMDH0R register  *******************/
#define  CAN_TXMDH0R_DATA4                   ((uint32_t)0x000000FF)        /* Data byte 4 */
#define  CAN_TXMDH0R_DATA5                   ((uint32_t)0x0000FF00)        /* Data byte 5 */
#define  CAN_TXMDH0R_DATA6                   ((uint32_t)0x00FF0000)        /* Data byte 6 */
#define  CAN_TXMDH0R_DATA7                   ((uint32_t)0xFF000000)        /* Data byte 7 */

/*******************  Bit definition for CAN_TXMI1R register  *******************/
#define  CAN_TXMI1R_TXRQ                     ((uint32_t)0x00000001)        /* Transmit Mailbox Request */
#define  CAN_TXMI1R_RTR                      ((uint32_t)0x00000002)        /* Remote Transmission Request */
#define  CAN_TXMI1R_IDE                      ((uint32_t)0x00000004)        /* Identifier Extension */
#define  CAN_TXMI1R_EXID                     ((uint32_t)0x001FFFF8)        /* Extended Identifier */
#define  CAN_TXMI1R_STID                     ((uint32_t)0xFFE00000)        /* Standard Identifier or Extended Identifier */

/*******************  Bit definition for CAN_TXMDT1R register  ******************/
#define  CAN_TXMDT1R_DLC                     ((uint32_t)0x0000000F)        /* Data Length Code */
#define  CAN_TXMDT1R_TGT                     ((uint32_t)0x00000100)        /* Transmit Global Time */
#define  CAN_TXMDT1R_TIME                    ((uint32_t)0xFFFF0000)        /* Message Time Stamp */

/*******************  Bit definition for CAN_TXMDL1R register  ******************/
#define  CAN_TXMDL1R_DATA0                   ((uint32_t)0x000000FF)        /* Data byte 0 */
#define  CAN_TXMDL1R_DATA1                   ((uint32_t)0x0000FF00)        /* Data byte 1 */
#define  CAN_TXMDL1R_DATA2                   ((uint32_t)0x00FF0000)        /* Data byte 2 */
#define  CAN_TXMDL1R_DATA3                   ((uint32_t)0xFF000000)        /* Data byte 3 */

/*******************  Bit definition for CAN_TXMDH1R register  ******************/
#define  CAN_TXMDH1R_DATA4                   ((uint32_t)0x000000FF)        /* Data byte 4 */
#define  CAN_TXMDH1R_DATA5                   ((uint32_t)0x0000FF00)        /* Data byte 5 */
#define  CAN_TXMDH1R_DATA6                   ((uint32_t)0x00FF0000)        /* Data byte 6 */
#define  CAN_TXMDH1R_DATA7                   ((uint32_t)0xFF000000)        /* Data byte 7 */

/*******************  Bit definition for CAN_TXMI2R register  *******************/
#define  CAN_TXMI2R_TXRQ                     ((uint32_t)0x00000001)        /* Transmit Mailbox Request */
#define  CAN_TXMI2R_RTR                      ((uint32_t)0x00000002)        /* Remote Transmission Request */
#define  CAN_TXMI2R_IDE                      ((uint32_t)0x00000004)        /* Identifier Extension */
#define  CAN_TXMI2R_EXID                     ((uint32_t)0x001FFFF8)        /* Extended identifier */
#define  CAN_TXMI2R_STID                     ((uint32_t)0xFFE00000)        /* Standard Identifier or Extended Identifier */

/*******************  Bit definition for CAN_TXMDT2R register  ******************/  
#define  CAN_TXMDT2R_DLC                     ((uint32_t)0x0000000F)        /* Data Length Code */
#define  CAN_TXMDT2R_TGT                     ((uint32_t)0x00000100)        /* Transmit Global Time */
#define  CAN_TXMDT2R_TIME                    ((uint32_t)0xFFFF0000)        /* Message Time Stamp */

/*******************  Bit definition for CAN_TXMDL2R register  ******************/
#define  CAN_TXMDL2R_DATA0                   ((uint32_t)0x000000FF)        /* Data byte 0 */
#define  CAN_TXMDL2R_DATA1                   ((uint32_t)0x0000FF00)        /* Data byte 1 */
#define  CAN_TXMDL2R_DATA2                   ((uint32_t)0x00FF0000)        /* Data byte 2 */
#define  CAN_TXMDL2R_DATA3                   ((uint32_t)0xFF000000)        /* Data byte 3 */

/*******************  Bit definition for CAN_TXMDH2R register  ******************/
#define  CAN_TXMDH2R_DATA4                   ((uint32_t)0x000000FF)        /* Data byte 4 */
#define  CAN_TXMDH2R_DATA5                   ((uint32_t)0x0000FF00)        /* Data byte 5 */
#define  CAN_TXMDH2R_DATA6                   ((uint32_t)0x00FF0000)        /* Data byte 6 */
#define  CAN_TXMDH2R_DATA7                   ((uint32_t)0xFF000000)        /* Data byte 7 */

/*******************  Bit definition for CAN_RXMI0R register  *******************/
#define  CAN_RXMI0R_RTR                      ((uint32_t)0x00000002)        /* Remote Transmission Request */
#define  CAN_RXMI0R_IDE                      ((uint32_t)0x00000004)        /* Identifier Extension */
#define  CAN_RXMI0R_EXID                     ((uint32_t)0x001FFFF8)        /* Extended Identifier */
#define  CAN_RXMI0R_STID                     ((uint32_t)0xFFE00000)        /* Standard Identifier or Extended Identifier */

/*******************  Bit definition for CAN_RXMDT0R register  ******************/
#define  CAN_RXMDT0R_DLC                     ((uint32_t)0x0000000F)        /* Data Length Code */
#define  CAN_RXMDT0R_FMI                     ((uint32_t)0x0000FF00)        /* Filter Match Index */
#define  CAN_RXMDT0R_TIME                    ((uint32_t)0xFFFF0000)        /* Message Time Stamp */

/*******************  Bit definition for CAN_RXMDL0R register  ******************/
#define  CAN_RXMDL0R_DATA0                   ((uint32_t)0x000000FF)        /* Data byte 0 */
#define  CAN_RXMDL0R_DATA1                   ((uint32_t)0x0000FF00)        /* Data byte 1 */
#define  CAN_RXMDL0R_DATA2                   ((uint32_t)0x00FF0000)        /* Data byte 2 */
#define  CAN_RXMDL0R_DATA3                   ((uint32_t)0xFF000000)        /* Data byte 3 */

/*******************  Bit definition for CAN_RXMDH0R register  ******************/
#define  CAN_RXMDH0R_DATA4                   ((uint32_t)0x000000FF)        /* Data byte 4 */
#define  CAN_RXMDH0R_DATA5                   ((uint32_t)0x0000FF00)        /* Data byte 5 */
#define  CAN_RXMDH0R_DATA6                   ((uint32_t)0x00FF0000)        /* Data byte 6 */
#define  CAN_RXMDH0R_DATA7                   ((uint32_t)0xFF000000)        /* Data byte 7 */

/*******************  Bit definition for CAN_RXMI1R register  *******************/
#define  CAN_RXMI1R_RTR                      ((uint32_t)0x00000002)        /* Remote Transmission Request */
#define  CAN_RXMI1R_IDE                      ((uint32_t)0x00000004)        /* Identifier Extension */
#define  CAN_RXMI1R_EXID                     ((uint32_t)0x001FFFF8)        /* Extended identifier */
#define  CAN_RXMI1R_STID                     ((uint32_t)0xFFE00000)        /* Standard Identifier or Extended Identifier */

/*******************  Bit definition for CAN_RXMDT1R register  ******************/
#define  CAN_RXMDT1R_DLC                     ((uint32_t)0x0000000F)        /* Data Length Code */
#define  CAN_RXMDT1R_FMI                     ((uint32_t)0x0000FF00)        /* Filter Match Index */
#define  CAN_RXMDT1R_TIME                    ((uint32_t)0xFFFF0000)        /* Message Time Stamp */

/*******************  Bit definition for CAN_RXMDL1R register  ******************/
#define  CAN_RXMDL1R_DATA0                   ((uint32_t)0x000000FF)        /* Data byte 0 */
#define  CAN_RXMDL1R_DATA1                   ((uint32_t)0x0000FF00)        /* Data byte 1 */
#define  CAN_RXMDL1R_DATA2                   ((uint32_t)0x00FF0000)        /* Data byte 2 */
#define  CAN_RXMDL1R_DATA3                   ((uint32_t)0xFF000000)        /* Data byte 3 */

/*******************  Bit definition for CAN_RXMDH1R register  ******************/
#define  CAN_RXMDH1R_DATA4                   ((uint32_t)0x000000FF)        /* Data byte 4 */
#define  CAN_RXMDH1R_DATA5                   ((uint32_t)0x0000FF00)        /* Data byte 5 */
#define  CAN_RXMDH1R_DATA6                   ((uint32_t)0x00FF0000)        /* Data byte 6 */
#define  CAN_RXMDH1R_DATA7                   ((uint32_t)0xFF000000)        /* Data byte 7 */

/*******************  Bit definition for CAN_FCTLR register  ********************/
#define  CAN_FCTLR_FINIT                     ((uint8_t)0x01)               /* Filter Init Mode */

/*******************  Bit definition for CAN_FMCFGR register  *******************/
#define  CAN_FMCFGR_FBM                      ((uint16_t)0x3FFF)            /* Filter Mode */
#define  CAN_FMCFGR_FBM0                     ((uint16_t)0x0001)            /* Filter Init Mode bit 0 */
#define  CAN_FMCFGR_FBM1                     ((uint16_t)0x0002)            /* Filter Init Mode bit 1 */
#define  CAN_FMCFGR_FBM2                     ((uint16_t)0x0004)            /* Filter Init Mode bit 2 */
#define  CAN_FMCFGR_FBM3                     ((uint16_t)0x0008)            /* Filter Init Mode bit 3 */
#define  CAN_FMCFGR_FBM4                     ((uint16_t)0x0010)            /* Filter Init Mode bit 4 */
#define  CAN_FMCFGR_FBM5                     ((uint16_t)0x0020)            /* Filter Init Mode bit 5 */
#define  CAN_FMCFGR_FBM6                     ((uint16_t)0x0040)            /* Filter Init Mode bit 6 */
#define  CAN_FMCFGR_FBM7                     ((uint16_t)0x0080)            /* Filter Init Mode bit 7 */
#define  CAN_FMCFGR_FBM8                     ((uint16_t)0x0100)            /* Filter Init Mode bit 8 */
#define  CAN_FMCFGR_FBM9                     ((uint16_t)0x0200)            /* Filter Init Mode bit 9 */
#define  CAN_FMCFGR_FBM10                    ((uint16_t)0x0400)            /* Filter Init Mode bit 10 */
#define  CAN_FMCFGR_FBM11                    ((uint16_t)0x0800)            /* Filter Init Mode bit 11 */
#define  CAN_FMCFGR_FBM12                    ((uint16_t)0x1000)            /* Filter Init Mode bit 12 */
#define  CAN_FMCFGR_FBM13                    ((uint16_t)0x2000)            /* Filter Init Mode bit 13 */

/*******************  Bit definition for CAN_FSCFGR register  *******************/
#define  CAN_FSCFGR_FSC                      ((uint16_t)0x3FFF)            /* Filter Scale Configuration */
#define  CAN_FSCFGR_FSC0                     ((uint16_t)0x0001)            /* Filter Scale Configuration bit 0 */
#define  CAN_FSCFGR_FSC1                     ((uint16_t)0x0002)            /* Filter Scale Configuration bit 1 */
#define  CAN_FSCFGR_FSC2                     ((uint16_t)0x0004)            /* Filter Scale Configuration bit 2 */
#define  CAN_FSCFGR_FSC3                     ((uint16_t)0x0008)            /* Filter Scale Configuration bit 3 */
#define  CAN_FSCFGR_FSC4                     ((uint16_t)0x0010)            /* Filter Scale Configuration bit 4 */
#define  CAN_FSCFGR_FSC5                     ((uint16_t)0x0020)            /* Filter Scale Configuration bit 5 */
#define  CAN_FSCFGR_FSC6                     ((uint16_t)0x0040)            /* Filter Scale Configuration bit 6 */
#define  CAN_FSCFGR_FSC7                     ((uint16_t)0x0080)            /* Filter Scale Configuration bit 7 */
#define  CAN_FSCFGR_FSC8                     ((uint16_t)0x0100)            /* Filter Scale Configuration bit 8 */
#define  CAN_FSCFGR_FSC9                     ((uint16_t)0x0200)            /* Filter Scale Configuration bit 9 */
#define  CAN_FSCFGR_FSC10                    ((uint16_t)0x0400)            /* Filter Scale Configuration bit 10 */
#define  CAN_FSCFGR_FSC11                    ((uint16_t)0x0800)            /* Filter Scale Configuration bit 11 */
#define  CAN_FSCFGR_FSC12                    ((uint16_t)0x1000)            /* Filter Scale Configuration bit 12 */
#define  CAN_FSCFGR_FSC13                    ((uint16_t)0x2000)            /* Filter Scale Configuration bit 13 */

/******************  Bit definition for CAN_FAFIFOR register  *******************/
#define  CAN_FAFIFOR_FFA                     ((uint16_t)0x3FFF)            /* Filter FIFO Assignment */
#define  CAN_FAFIFOR_FFA0                    ((uint16_t)0x0001)            /* Filter FIFO Assignment for Filter 0 */
#define  CAN_FAFIFOR_FFA1                    ((uint16_t)0x0002)            /* Filter FIFO Assignment for Filter 1 */
#define  CAN_FAFIFOR_FFA2                    ((uint16_t)0x0004)            /* Filter FIFO Assignment for Filter 2 */
#define  CAN_FAFIFOR_FFA3                    ((uint16_t)0x0008)            /* Filter FIFO Assignment for Filter 3 */
#define  CAN_FAFIFOR_FFA4                    ((uint16_t)0x0010)            /* Filter FIFO Assignment for Filter 4 */
#define  CAN_FAFIFOR_FFA5                    ((uint16_t)0x0020)            /* Filter FIFO Assignment for Filter 5 */
#define  CAN_FAFIFOR_FFA6                    ((uint16_t)0x0040)            /* Filter FIFO Assignment for Filter 6 */
#define  CAN_FAFIFOR_FFA7                    ((uint16_t)0x0080)            /* Filter FIFO Assignment for Filter 7 */
#define  CAN_FAFIFOR_FFA8                    ((uint16_t)0x0100)            /* Filter FIFO Assignment for Filter 8 */
#define  CAN_FAFIFOR_FFA9                    ((uint16_t)0x0200)            /* Filter FIFO Assignment for Filter 9 */
#define  CAN_FAFIFOR_FFA10                   ((uint16_t)0x0400)            /* Filter FIFO Assignment for Filter 10 */
#define  CAN_FAFIFOR_FFA11                   ((uint16_t)0x0800)            /* Filter FIFO Assignment for Filter 11 */
#define  CAN_FAFIFOR_FFA12                   ((uint16_t)0x1000)            /* Filter FIFO Assignment for Filter 12 */
#define  CAN_FAFIFOR_FFA13                   ((uint16_t)0x2000)            /* Filter FIFO Assignment for Filter 13 */

/*******************  Bit definition for CAN_FWR register  *******************/
#define  CAN_FWR_FACT                        ((uint16_t)0x3FFF)            /* Filter Active */
#define  CAN_FWR_FACT0                       ((uint16_t)0x0001)            /* Filter 0 Active */
#define  CAN_FWR_FACT1                       ((uint16_t)0x0002)            /* Filter 1 Active */
#define  CAN_FWR_FACT2                       ((uint16_t)0x0004)            /* Filter 2 Active */
#define  CAN_FWR_FACT3                       ((uint16_t)0x0008)            /* Filter 3 Active */
#define  CAN_FWR_FACT4                       ((uint16_t)0x0010)            /* Filter 4 Active */
#define  CAN_FWR_FACT5                       ((uint16_t)0x0020)            /* Filter 5 Active */
#define  CAN_FWR_FACT6                       ((uint16_t)0x0040)            /* Filter 6 Active */
#define  CAN_FWR_FACT7                       ((uint16_t)0x0080)            /* Filter 7 Active */
#define  CAN_FWR_FACT8                       ((uint16_t)0x0100)            /* Filter 8 Active */
#define  CAN_FWR_FACT9                       ((uint16_t)0x0200)            /* Filter 9 Active */
#define  CAN_FWR_FACT10                      ((uint16_t)0x0400)            /* Filter 10 Active */
#define  CAN_FWR_FACT11                      ((uint16_t)0x0800)            /* Filter 11 Active */
#define  CAN_FWR_FACT12                      ((uint16_t)0x1000)            /* Filter 12 Active */
#define  CAN_FWR_FACT13                      ((uint16_t)0x2000)            /* Filter 13 Active */

/*******************  Bit definition for CAN_F0R1 register  *******************/
#define  CAN_F0R1_FB0                        ((uint32_t)0x00000001)        /* Filter bit 0 */
#define  CAN_F0R1_FB1                        ((uint32_t)0x00000002)        /* Filter bit 1 */
#define  CAN_F0R1_FB2                        ((uint32_t)0x00000004)        /* Filter bit 2 */
#define  CAN_F0R1_FB3                        ((uint32_t)0x00000008)        /* Filter bit 3 */
#define  CAN_F0R1_FB4                        ((uint32_t)0x00000010)        /* Filter bit 4 */
#define  CAN_F0R1_FB5                        ((uint32_t)0x00000020)        /* Filter bit 5 */
#define  CAN_F0R1_FB6                        ((uint32_t)0x00000040)        /* Filter bit 6 */
#define  CAN_F0R1_FB7                        ((uint32_t)0x00000080)        /* Filter bit 7 */
#define  CAN_F0R1_FB8                        ((uint32_t)0x00000100)        /* Filter bit 8 */
#define  CAN_F0R1_FB9                        ((uint32_t)0x00000200)        /* Filter bit 9 */
#define  CAN_F0R1_FB10                       ((uint32_t)0x00000400)        /* Filter bit 10 */
#define  CAN_F0R1_FB11                       ((uint32_t)0x00000800)        /* Filter bit 11 */
#define  CAN_F0R1_FB12                       ((uint32_t)0x00001000)        /* Filter bit 12 */
#define  CAN_F0R1_FB13                       ((uint32_t)0x00002000)        /* Filter bit 13 */
#define  CAN_F0R1_FB14                       ((uint32_t)0x00004000)        /* Filter bit 14 */
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
#define  CAN_F2R1_FB23                       ((uint32_t)0x00800000)        /* Filter bit 23 */
#define  CAN_F2R1_FB24                       ((uint32_t)0x01000000)        /* Filter bit 24 */
#define  CAN_F2R1_FB25                       ((uint32_t)0x02000000)        /* Filter bit 25 */
#define  CAN_F2R1_FB26                       ((uint32_t)0x04000000)        /* Filter bit 26 */
#define  CAN_F2R1_FB27                       ((uint32_t)0x08000000)        /* Filter bit 27 */
#define  CAN_F2R1_FB28                       ((uint32_t)0x10000000)        /* Filter bit 28 */
#define  CAN_F2R1_FB29                       ((uint32_t)0x20000000)        /* Filter bit 29 */
#define  CAN_F2R1_FB30                       ((uint32_t)0x40000000)        /* Filter bit 30 */
#define  CAN_F2R1_FB31                       ((uint32_t)0x80000000)        /* Filter bit 31 */
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
